svgeesus/EuroMPE/Polyphonic/voltage-ref-MAX6226ALA50+.md

# Voltage ref MAX6226ALA50+ 

New, hermetic ceramic LCC-8 package, may be replacing MAX6126AASA50+? Similar specs (but no ground sense, only output sense). Actually in stock at Mouser. $11.79/1

## Absolute initial accuracy

Initial accuracy 0.02% max = 1mV.

## Temperature

3ppm/°C (Max)

## Current / Load

Load regulation 5 (typ) 50 (max) μV/mA

## Long term drift

11ppm/1000hr

## Line regulation

Low dropout, 200mV, can run from 5.5V
