svgeesus/EuroMPE/Duophonic/notes.txt

High (120ms) latency on Teensy 4 with software MIDI-through
https://forum.pjrc.com/threads/65205-MIDI-Passthrough-Control-with-Op-Amp
