svgeesus/EuroMPE/data/oscillators/Tona.md

# Tona frequency analysis

## Tunng range (0V CV)

Coarse mid-way,
    fine mid-way, no external CV
        778.9Hz sd 1.8Hz
        G5 minus 11 cents
        maybe picking up periodic interference from nearby phaser.

    fine at min
        662.0Hz, sd 43mHz
        E5 plus 7 cents

    fine at max
        924.6Hz, sd 65mHz
        A#5 minus 14 cents

    fine range log2(f2/f1) =

Coarse at min
    fine at min, no ext CV
        2.40Hz, sd 66mHz
        D#-3 minus 22 cents

Coarse at max
    fine at max
        66.15kHz, sd 8.6
        rising trend,
