svgeesus/EuroMPE/data/oscillators/A111-3.md

# Doepfer A111-3 VCO

0.0030V 31.99896Hz  -> 5 octaves up is 1023.96672Hz
5.0030V 1022288Hz
1023.9963 at 5.0055V

5.0025 / 5 = 1.0005 V/octaves
