svgeesus/EuroMPE/data/oscillators/Dixie2plus.md

# Intellijel Dixie 2+ VCO

Warmed > 24 hours.

T=24.5C

0.0094V 31.99636Hz  -> 5 octaves up is 1023.88352Hz
5.0094V 1029.656Hz
1024.0593 at 5.0016V (too high, check for closer to 1023.88352Hz)

4.9922 / 5 = 0.99844 V/octaves
