svgeesus/EuroMPE/data/oscillators/Dixie2-audiorange.png

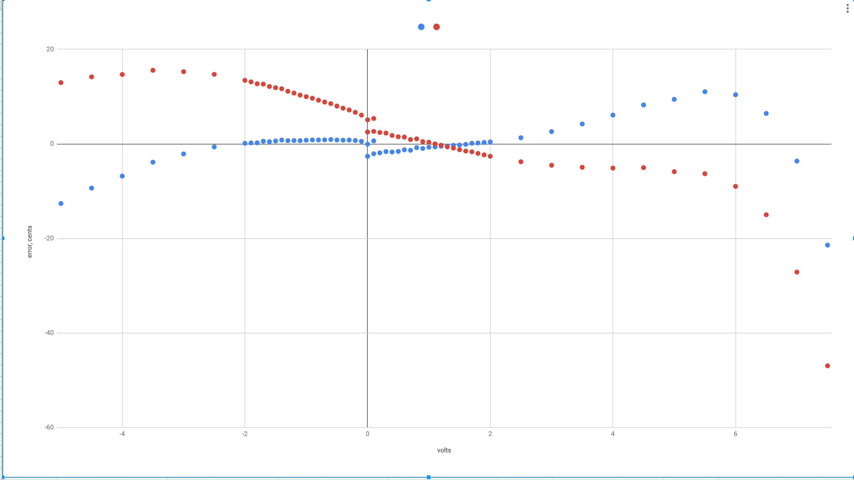
data/oscillators/Dixie2-audiorange.png
