svgeesus/EuroMPE/data/oscillators/Dixie2-fullrange.png

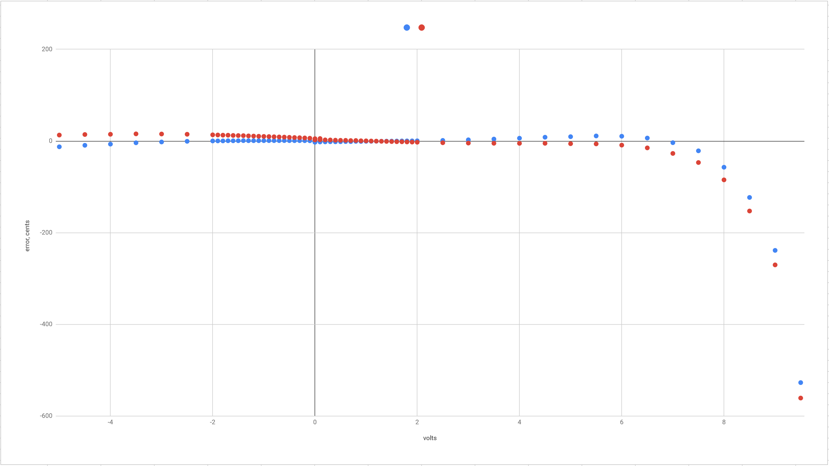
data/oscillators/Dixie2-fullrange.png
