svgeesus/EuroMPE/data/oscillators/Tona HF warmedup.png

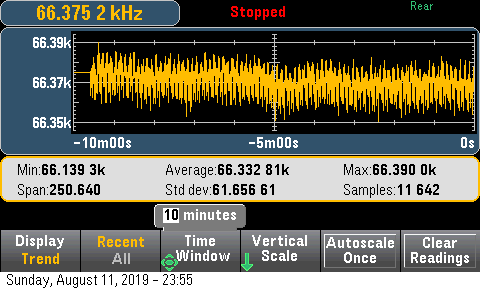
data/oscillators/Tona HF warmedup.png
