svgeesus/EuroMPE/Duophonic/img/10R.png

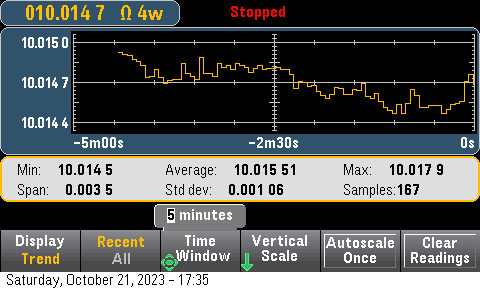
Duophonic/img/10R.png
