svgeesus/EuroMPE/Duophonic/img/1236-2-neg-next37hr.png

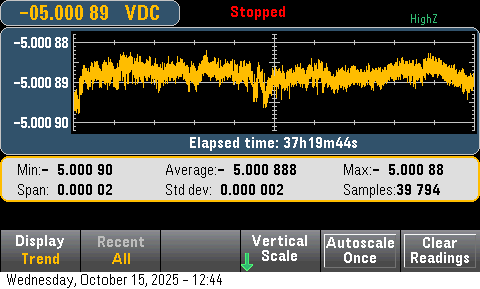
Duophonic/img/1236-2-neg-next37hr.png
