svgeesus/EuroMPE/Duophonic/img/1236-neg-13h.png

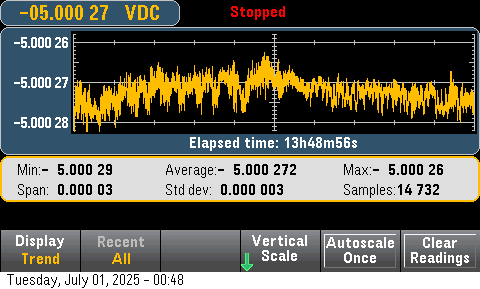
Duophonic/img/1236-neg-13h.png
