svgeesus/EuroMPE/Duophonic/img/adafruit-soft-touch-push.png

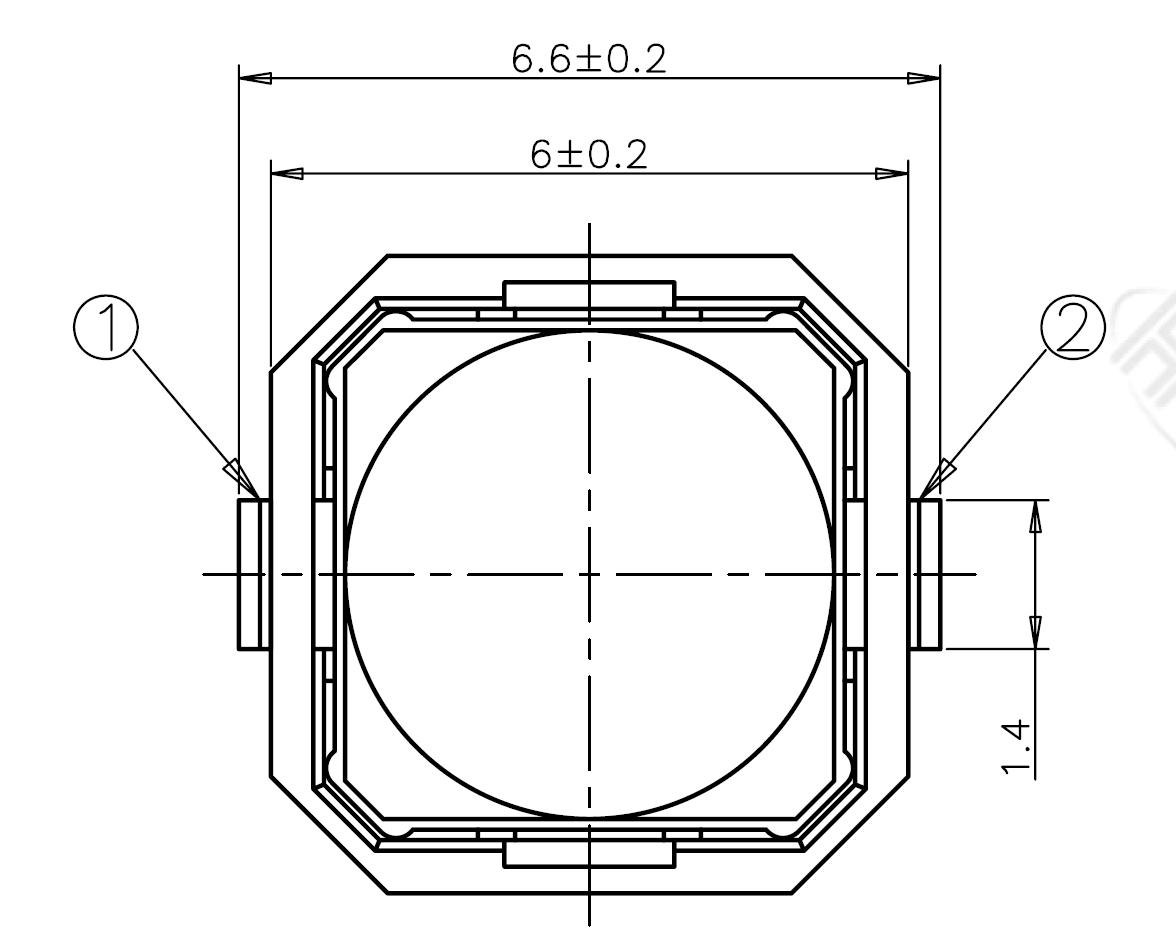
Duophonic/img/adafruit-soft-touch-push.png
