svgeesus/EuroMPE/Duophonic/img/Adafruit-USB-B-panel.png

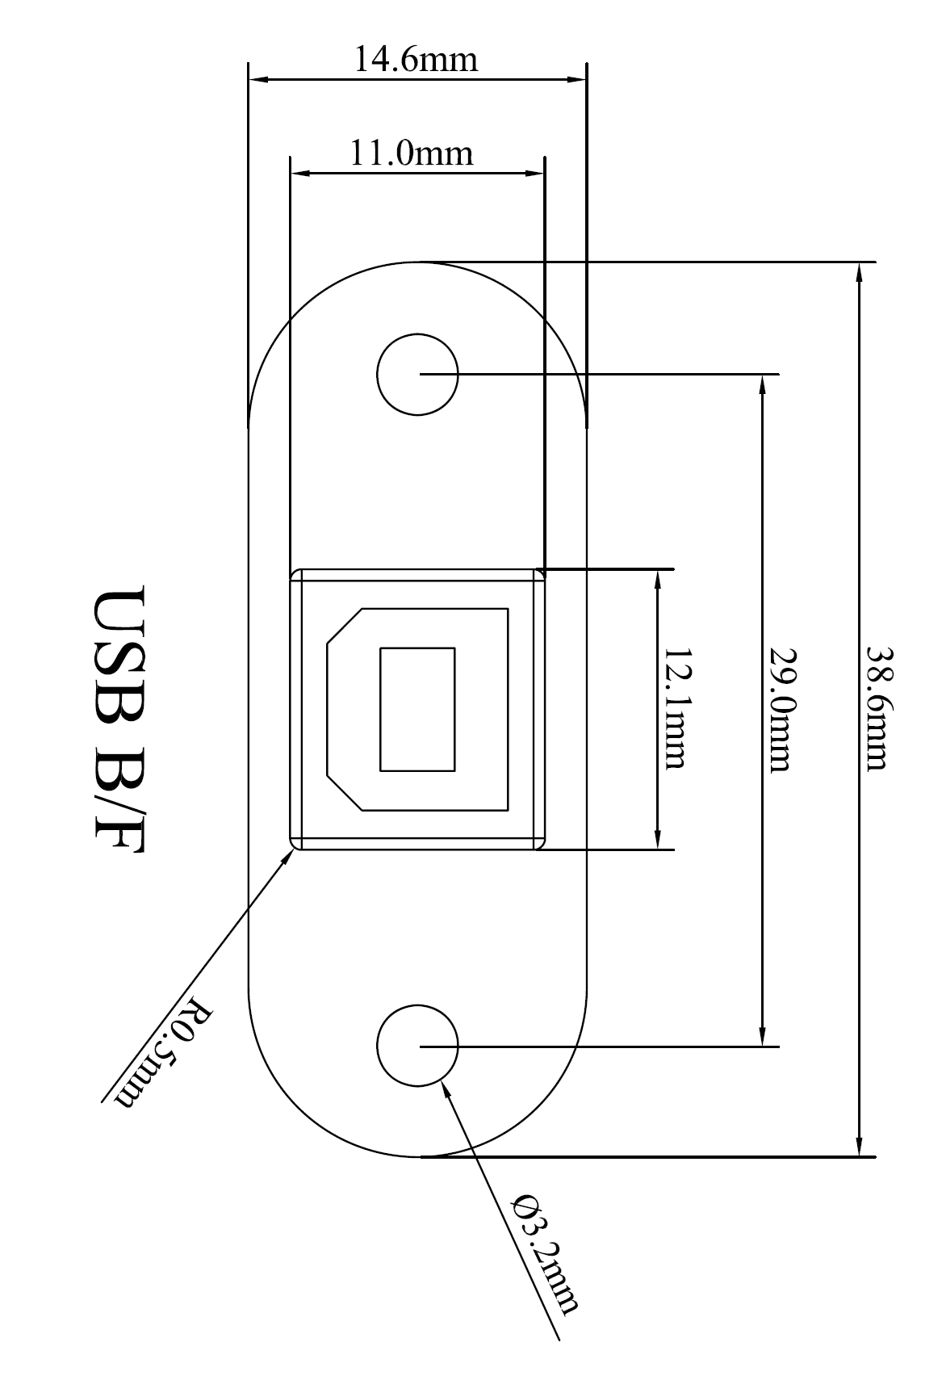
Duophonic/img/Adafruit-USB-B-panel.png
