svgeesus/EuroMPE/Duophonic/img/Adafruit-USB-B-photo.jpg

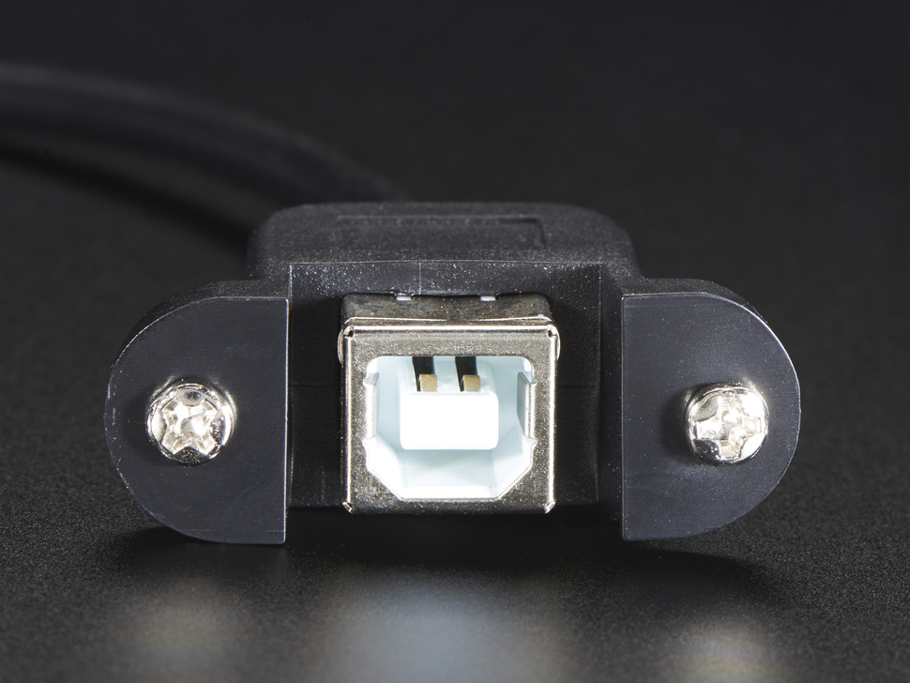
Duophonic/img/Adafruit-USB-B-photo.jpg
