svgeesus/EuroMPE/Duophonic/img/analogled.jpg

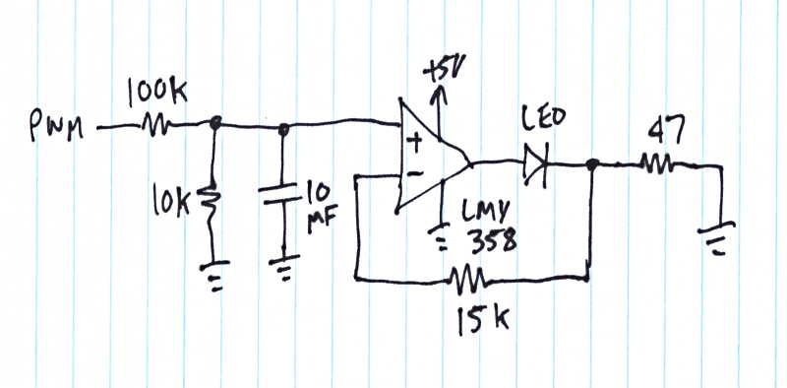
Duophonic/img/analogled.jpg
