svgeesus/EuroMPE/Duophonic/img/CKtactile.png

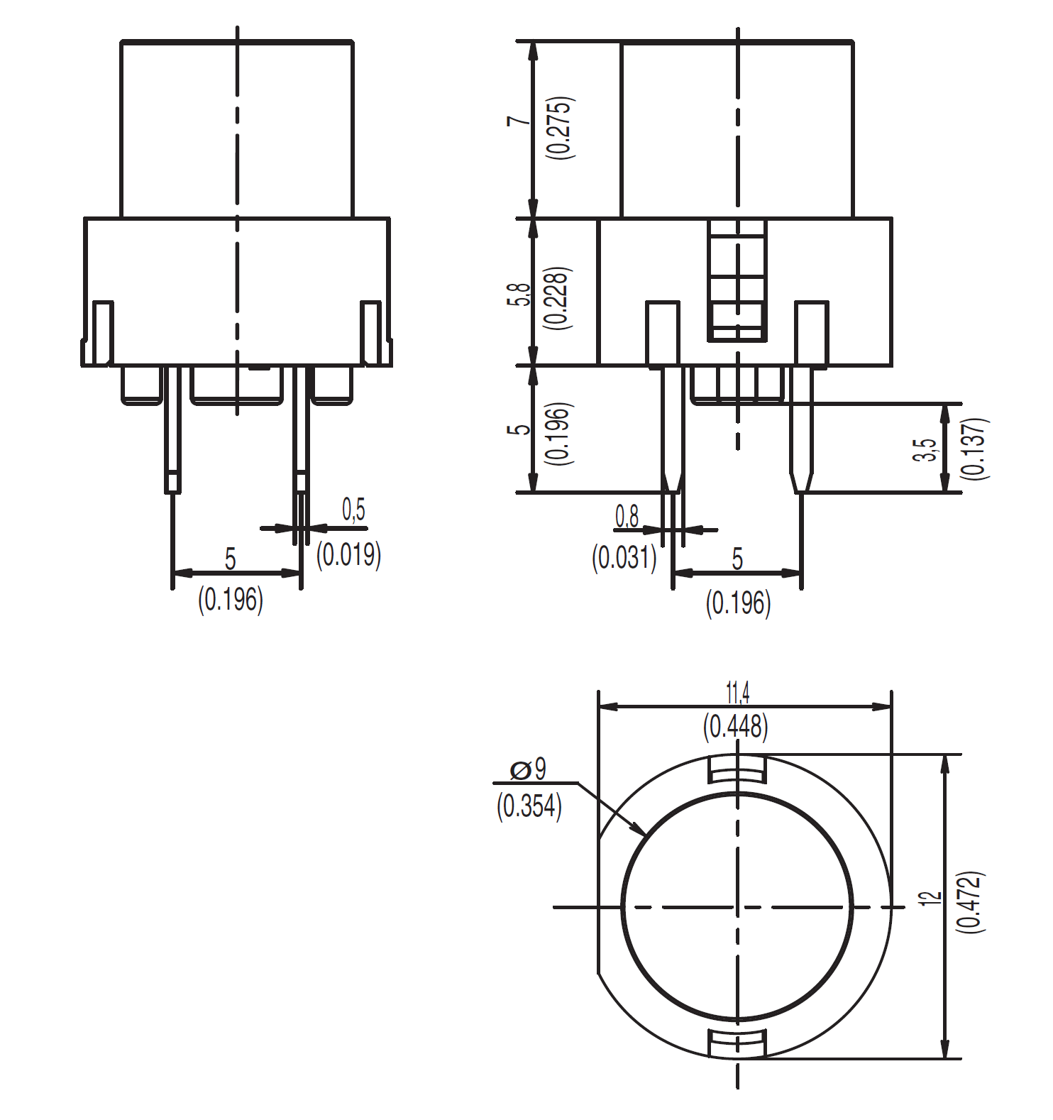
Duophonic/img/CKtactile.png
