svgeesus/EuroMPE/Duophonic/img/cvout-6n8-10k-200p.png

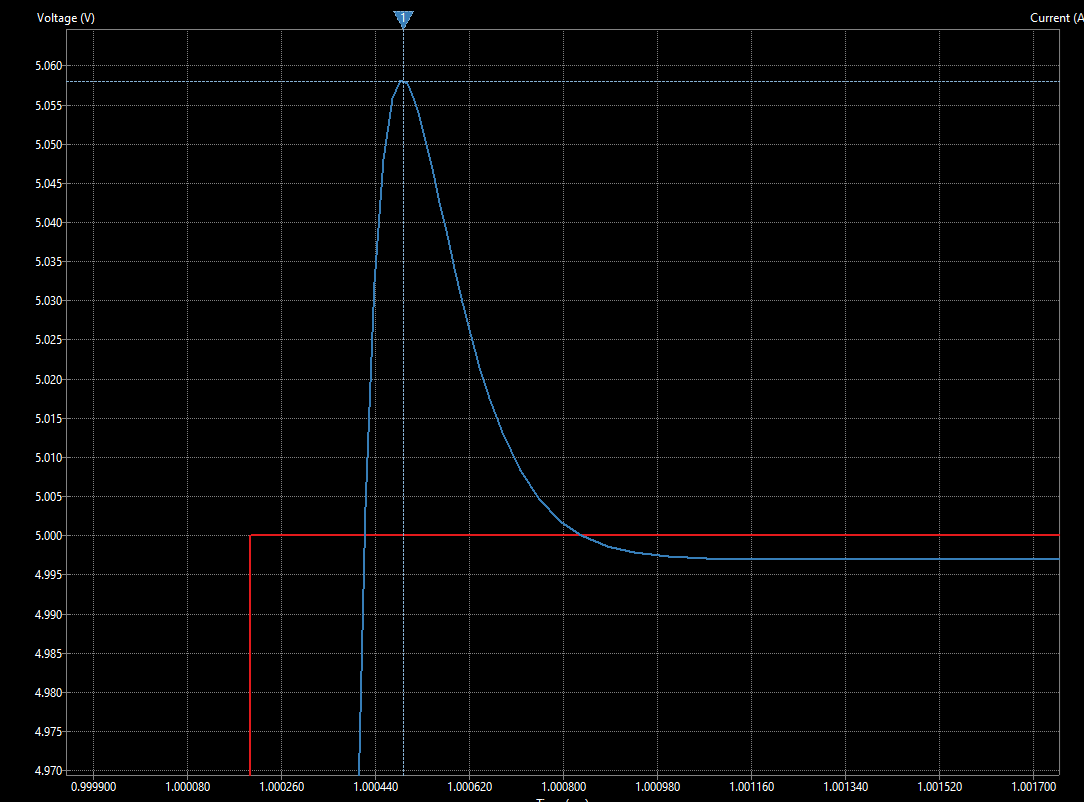
Duophonic/img/cvout-6n8-10k-200p.png
