svgeesus/EuroMPE/Duophonic/img/cvout-100n-200pF.png

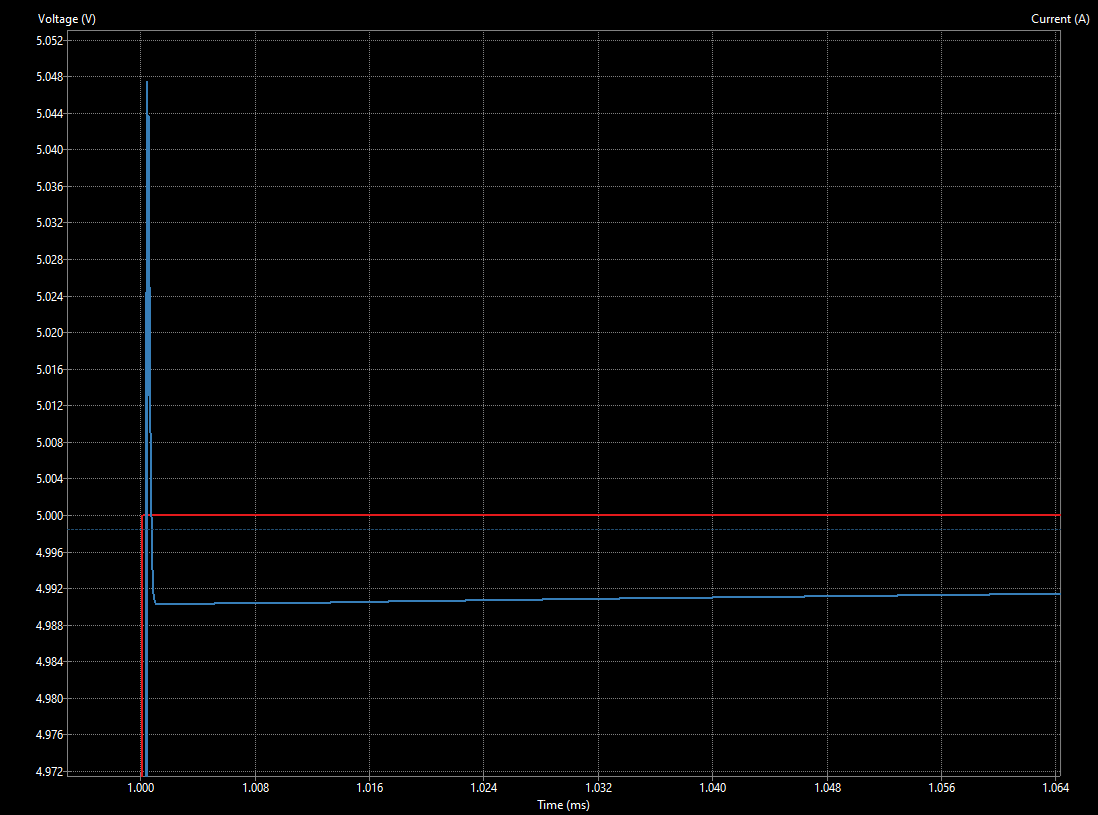
Duophonic/img/cvout-100n-200pF.png
