svgeesus/EuroMPE/Duophonic/img/DAC8168-14-pinout.png

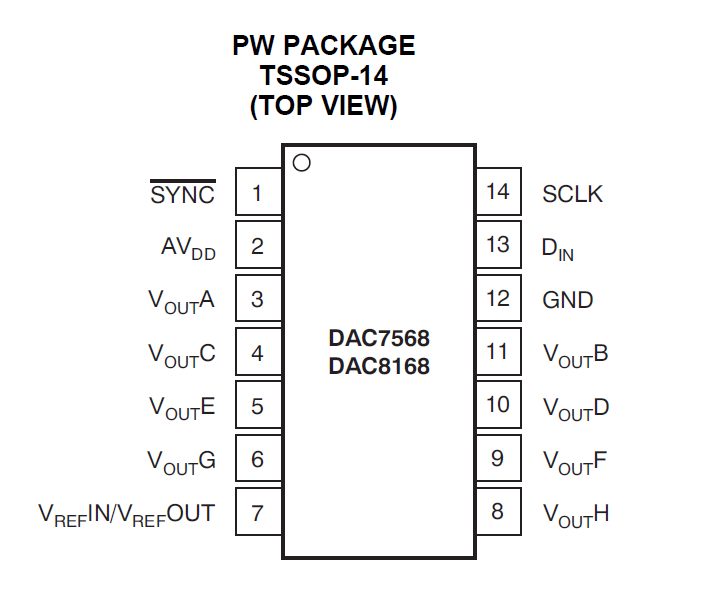
Duophonic/img/DAC8168-14-pinout.png
