svgeesus/EuroMPE/Duophonic/img/Encoder-Sparkfun-RGB.png

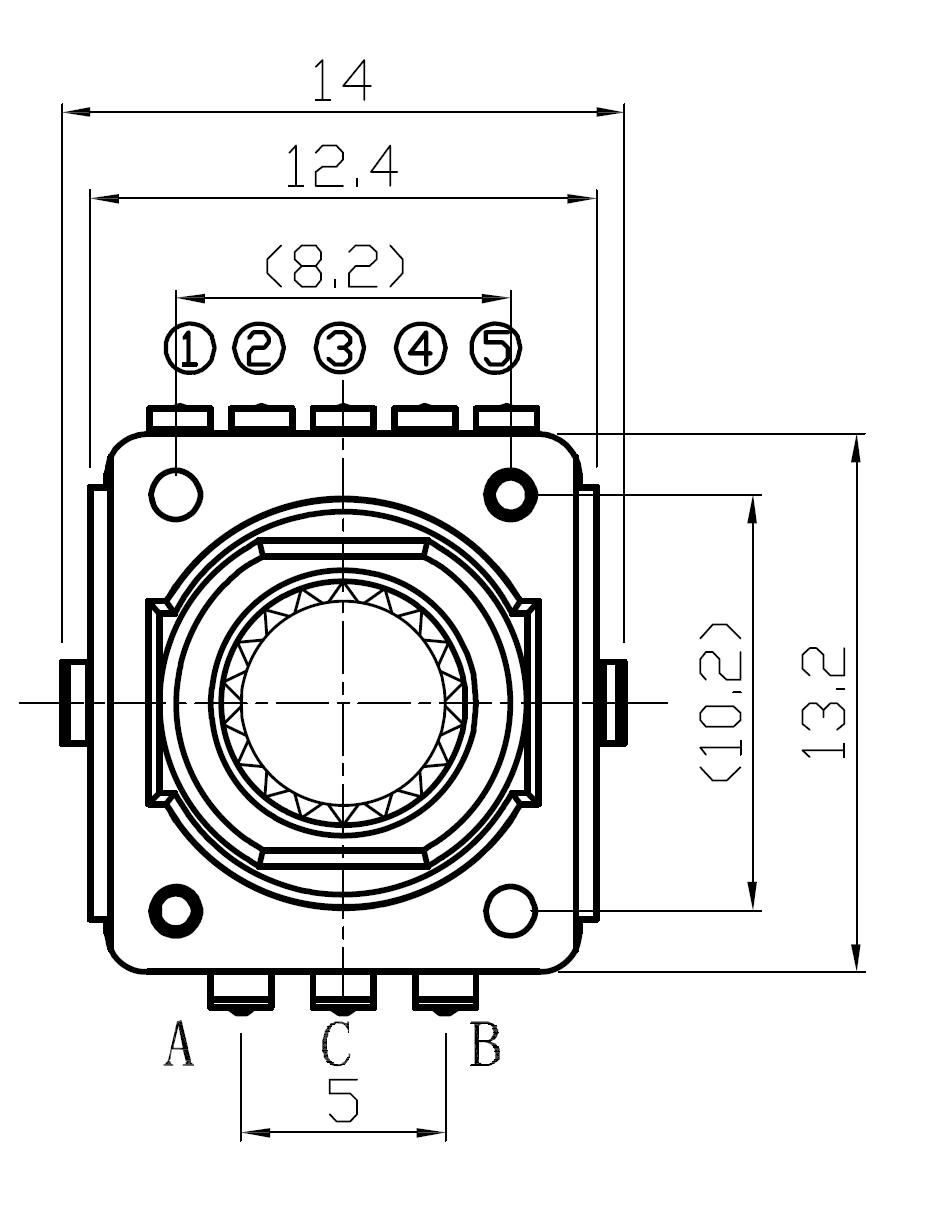
Duophonic/img/Encoder-Sparkfun-RGB.png
