svgeesus/EuroMPE/Duophonic/img/FD-115TRGB.png

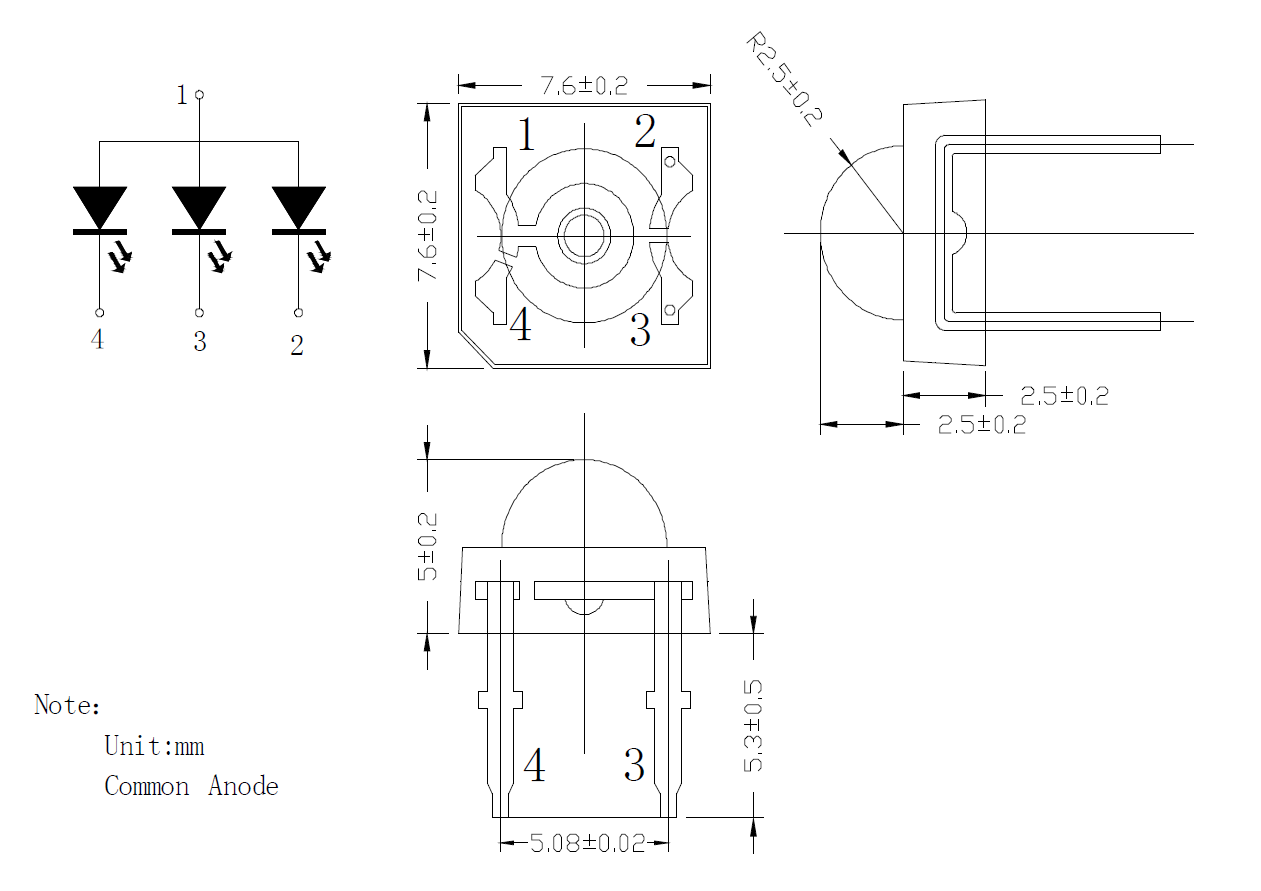
Duophonic/img/FD-115TRGB.png
