svgeesus/EuroMPE/Duophonic/img/front.png

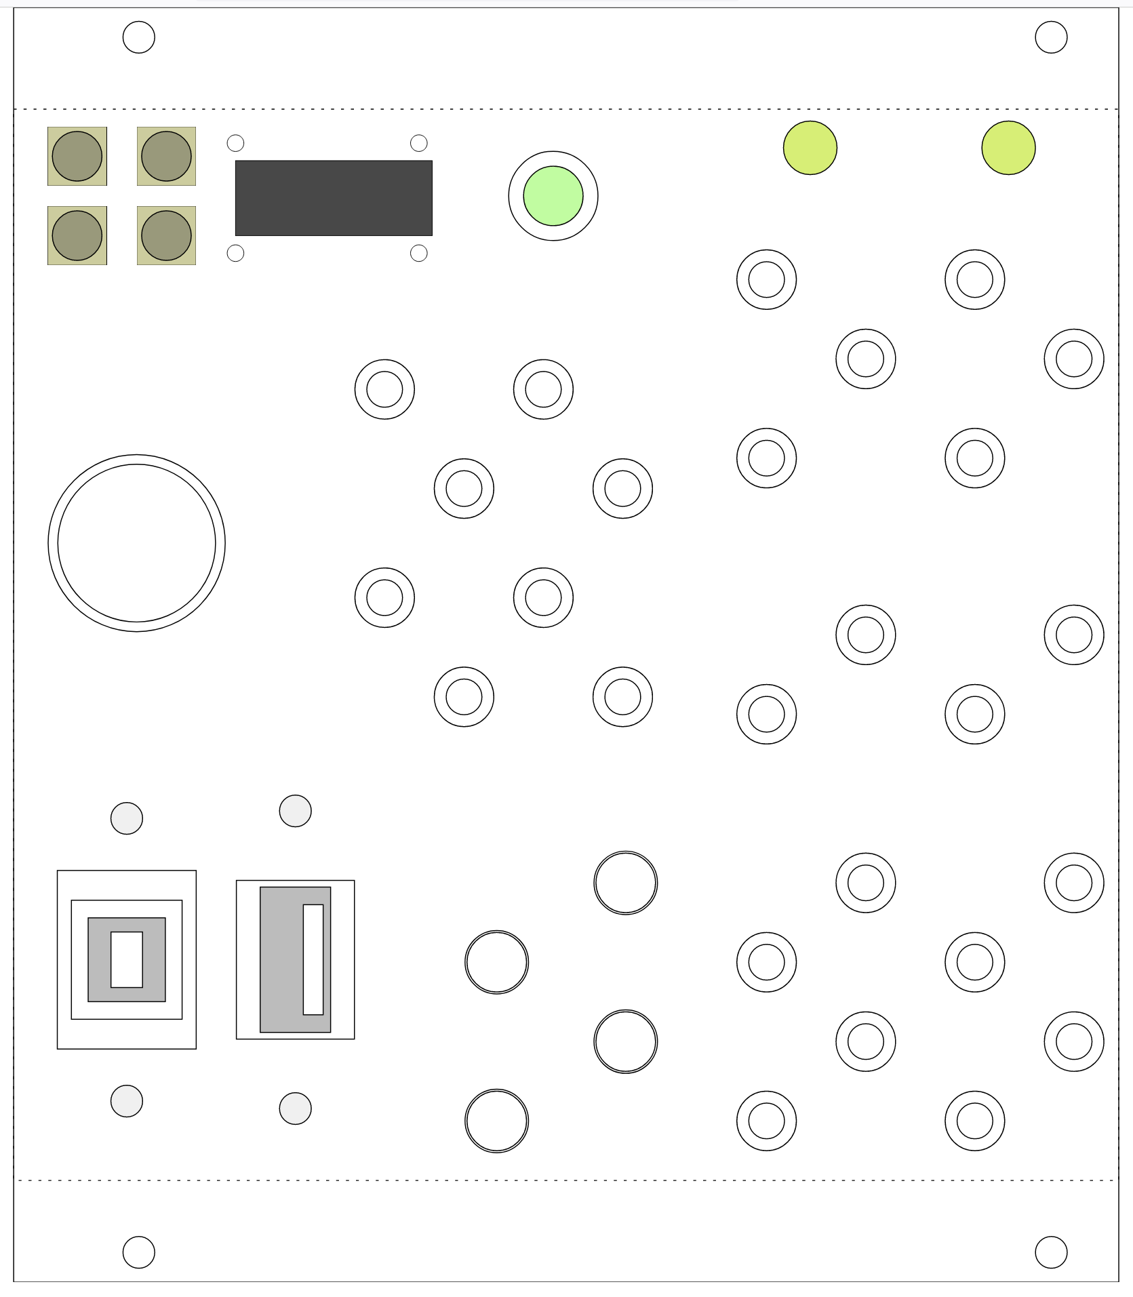
Duophonic/img/front.png
