svgeesus/EuroMPE/Duophonic/img/LS8-trim-circuit.png

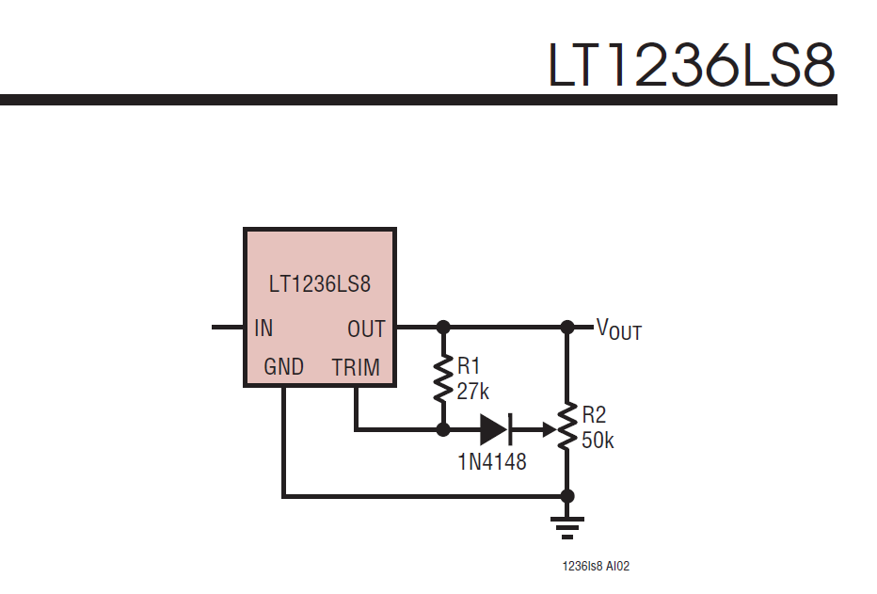
Duophonic/img/LS8-trim-circuit.png
