svgeesus/EuroMPE/Duophonic/img/LS8-trim-text.png

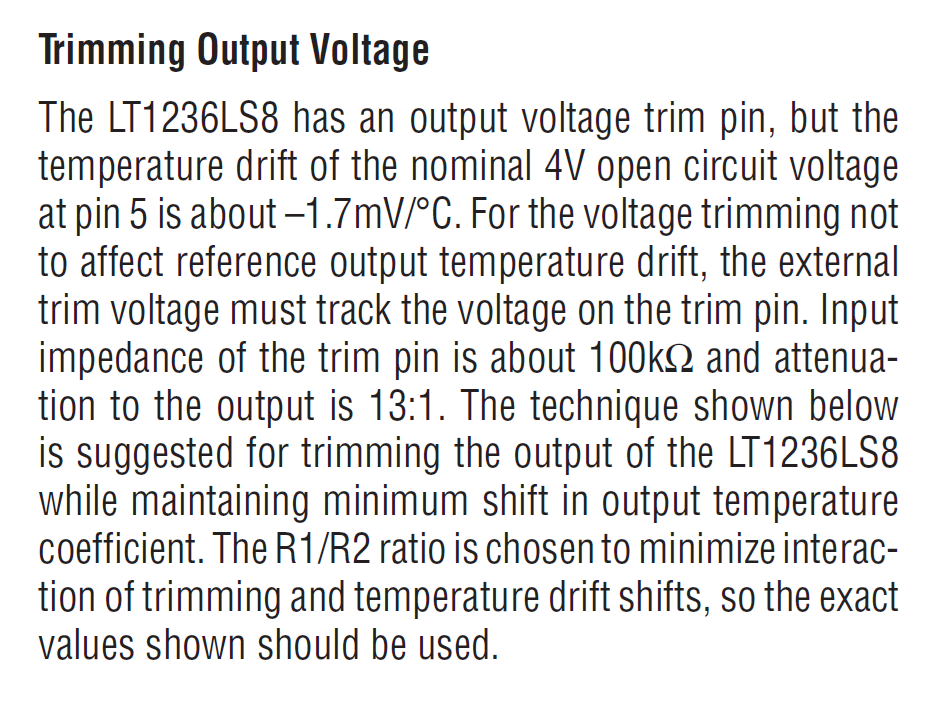
Duophonic/img/LS8-trim-text.png
