svgeesus/EuroMPE/Duophonic/img/MPU-mockup.png

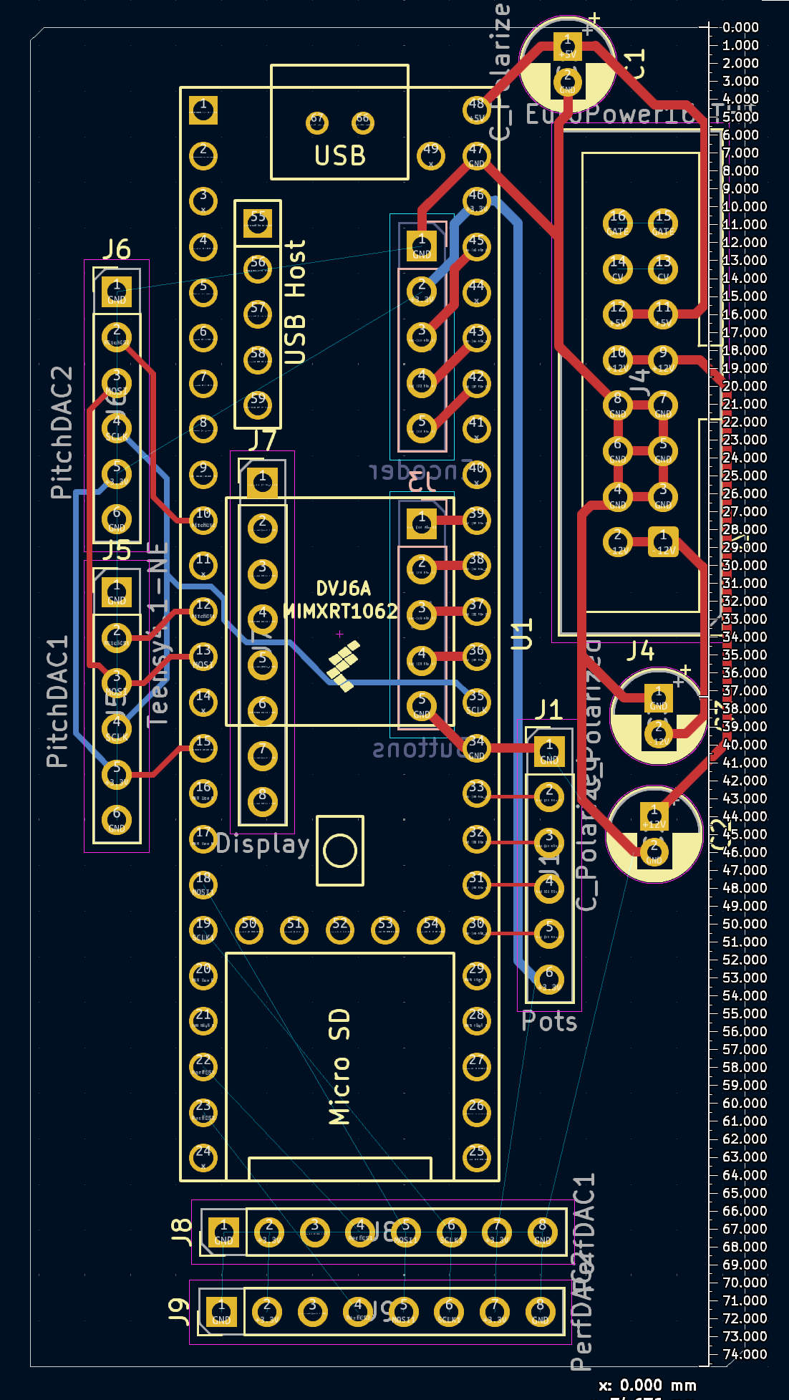
Duophonic/img/MPU-mockup.png
