svgeesus/EuroMPE/Duophonic/img/O_C-T41 output_buffer.png

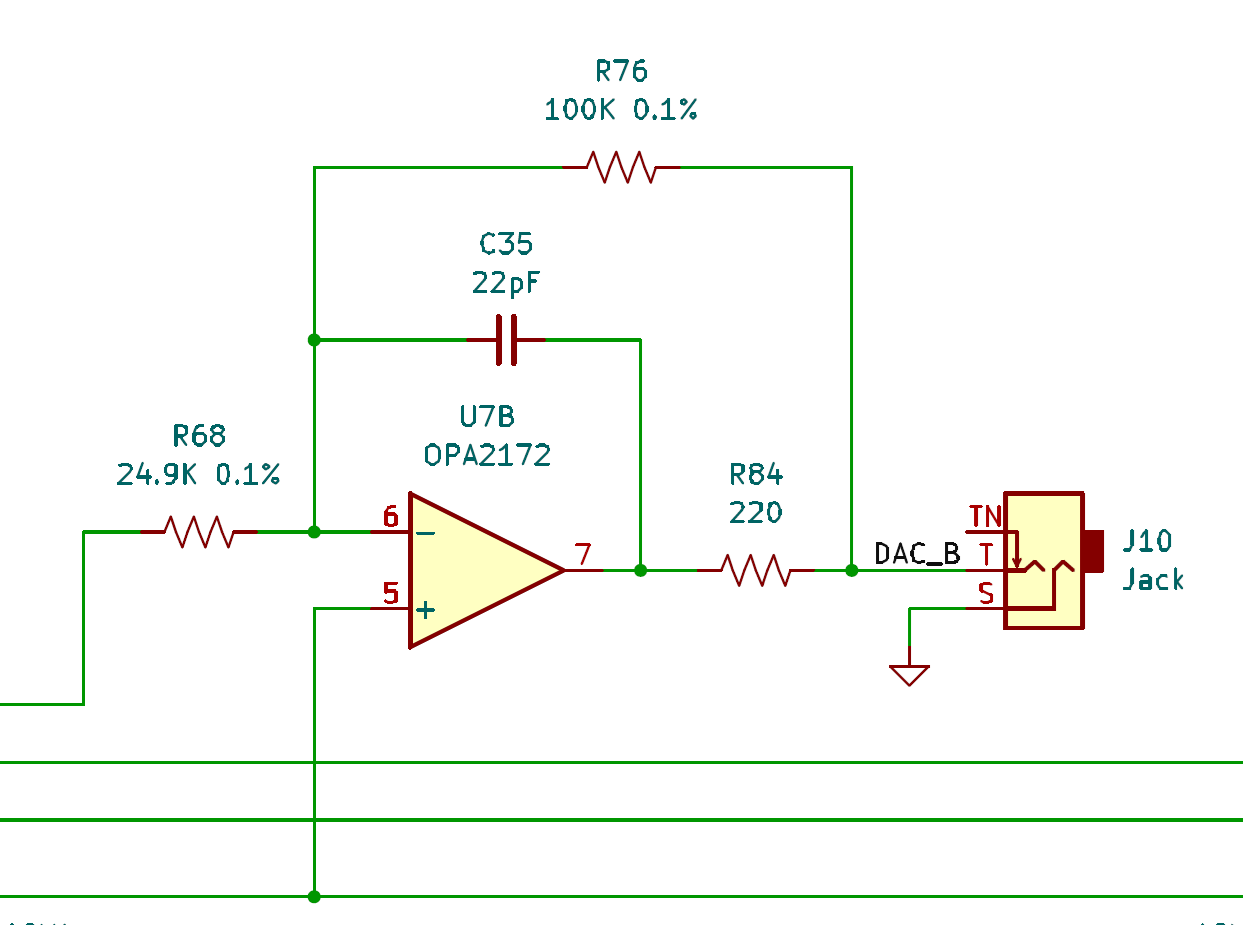
Duophonic/img/O_C-T41 output_buffer.png
