svgeesus/EuroMPE/Duophonic/img/oled-panel.png

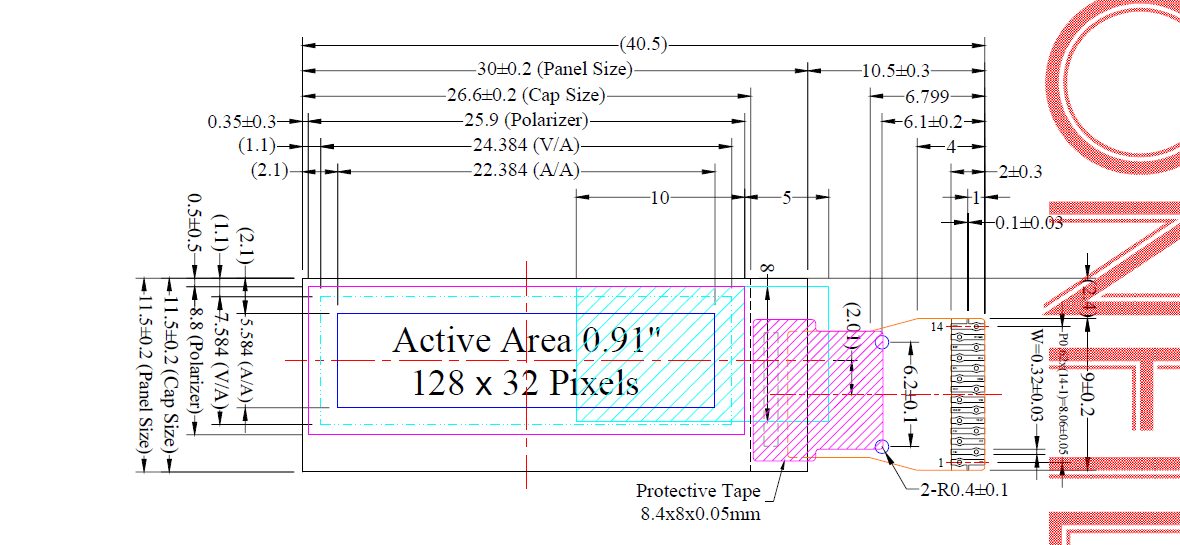
Duophonic/img/oled-panel.png
