svgeesus/EuroMPE/Duophonic/img/PerfDAC-v2-bottom-osh.png

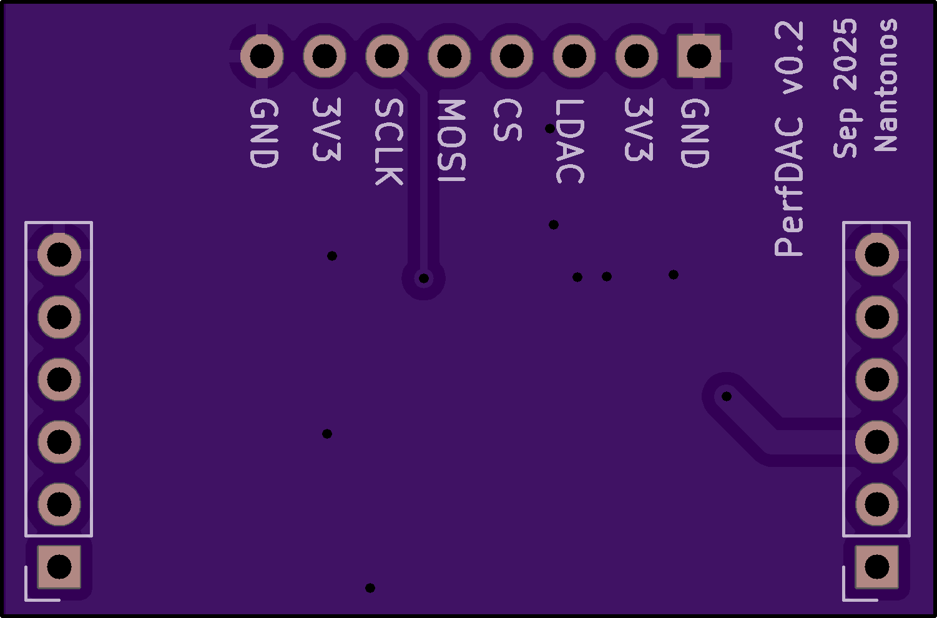
Duophonic/img/PerfDAC-v2-bottom-osh.png
