svgeesus/EuroMPE/Duophonic/img/PerfDAC-v2-top-osh.png

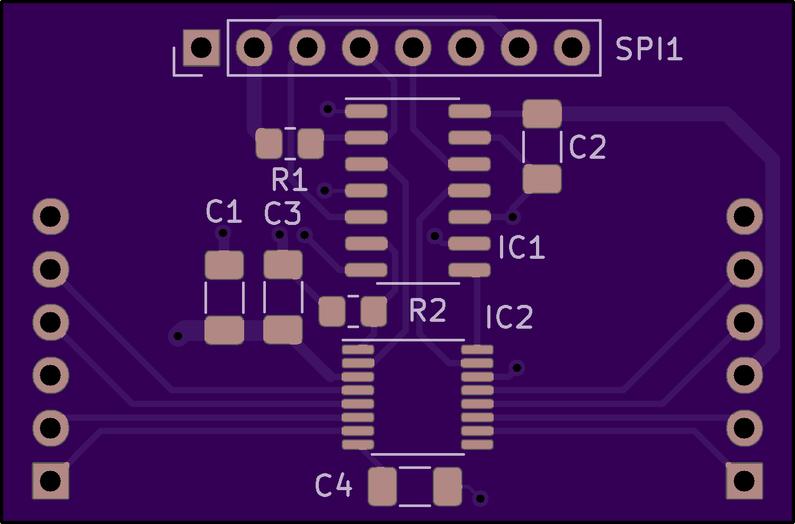
Duophonic/img/PerfDAC-v2-top-osh.png
