svgeesus/EuroMPE/Duophonic/img/pinout-41.png

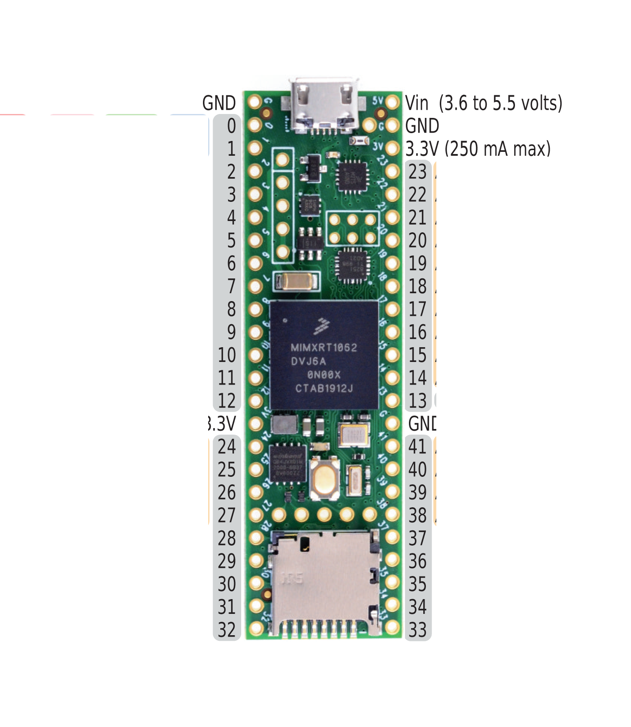
Duophonic/img/pinout-41.png
