svgeesus/EuroMPE/Duophonic/img/pitchdac-board.png

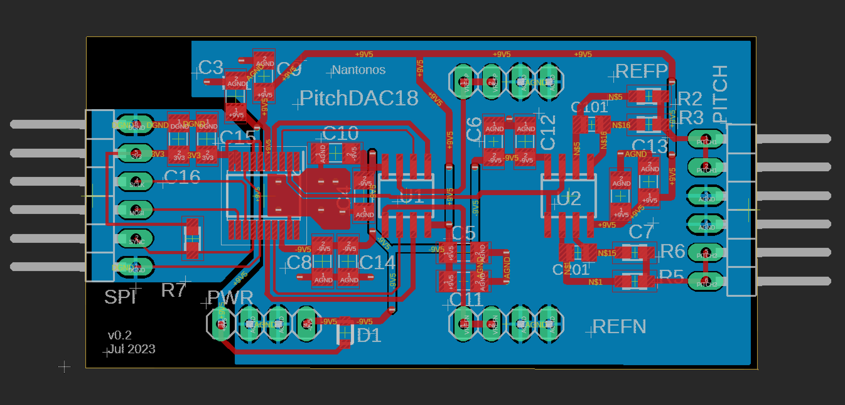
Duophonic/img/pitchdac-board.png
