svgeesus/EuroMPE/Duophonic/img/pitchdac-schematic-v04.png

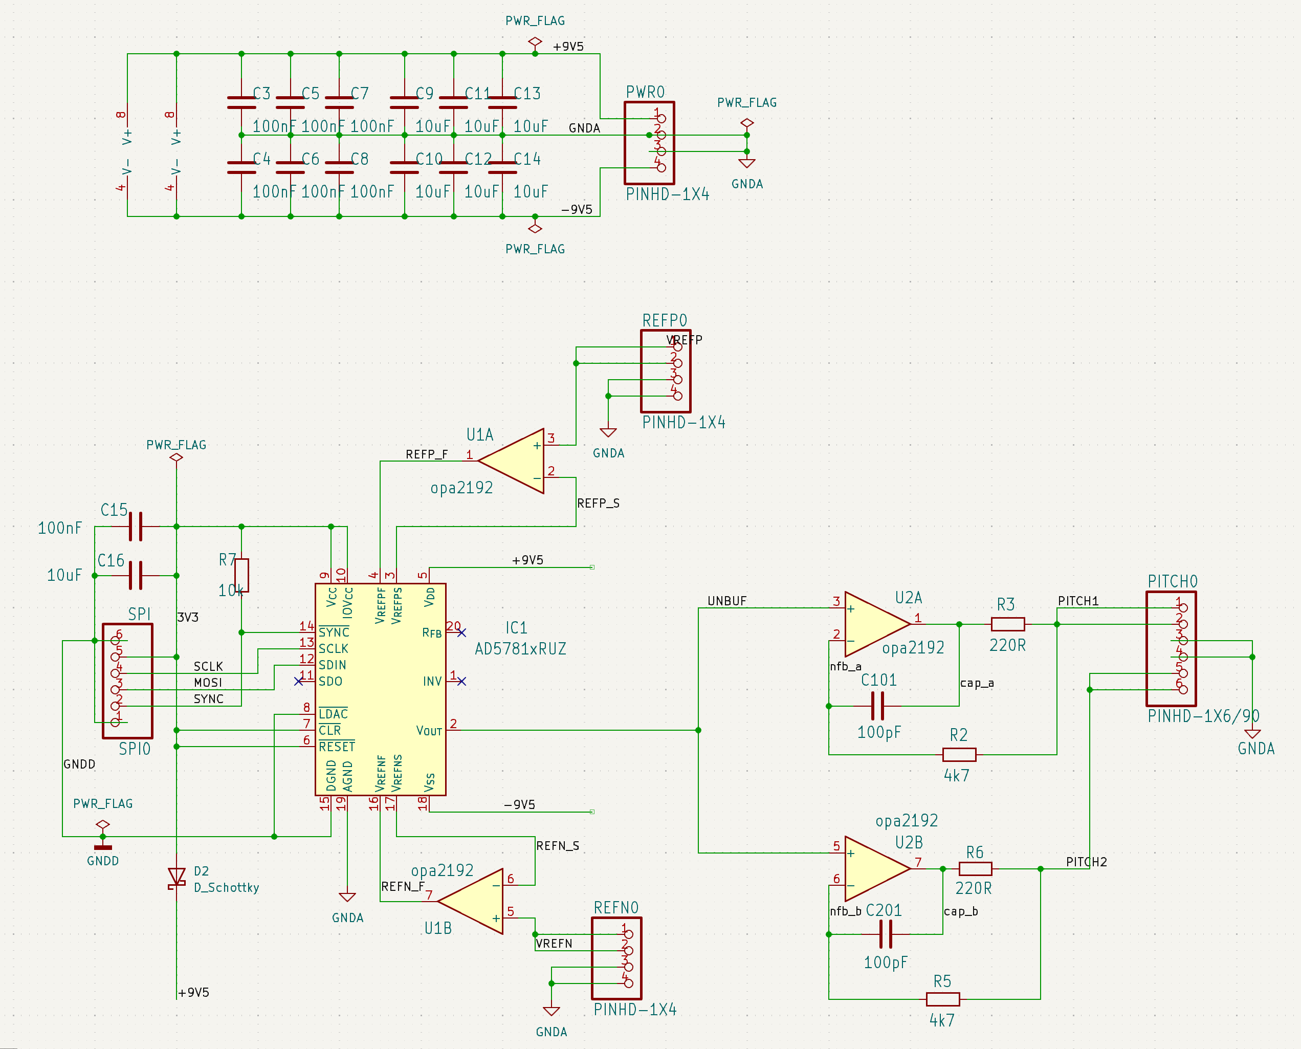
Duophonic/img/pitchdac-schematic-v04.png
