svgeesus/EuroMPE/Duophonic/img/pitchdac-top-osh.png

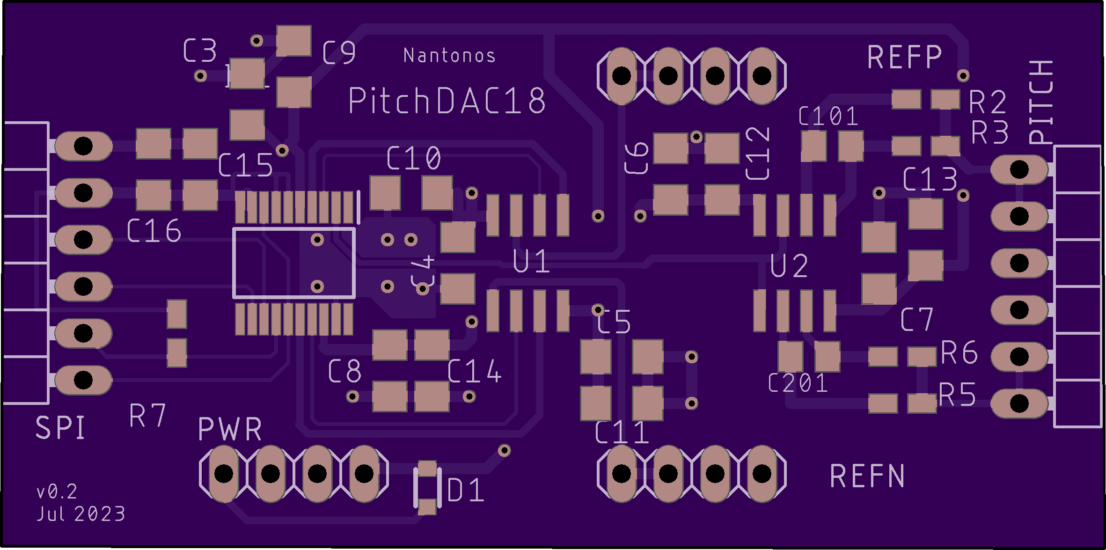
Duophonic/img/pitchdac-top-osh.png
