svgeesus/EuroMPE/Duophonic/img/power-osh-back.png

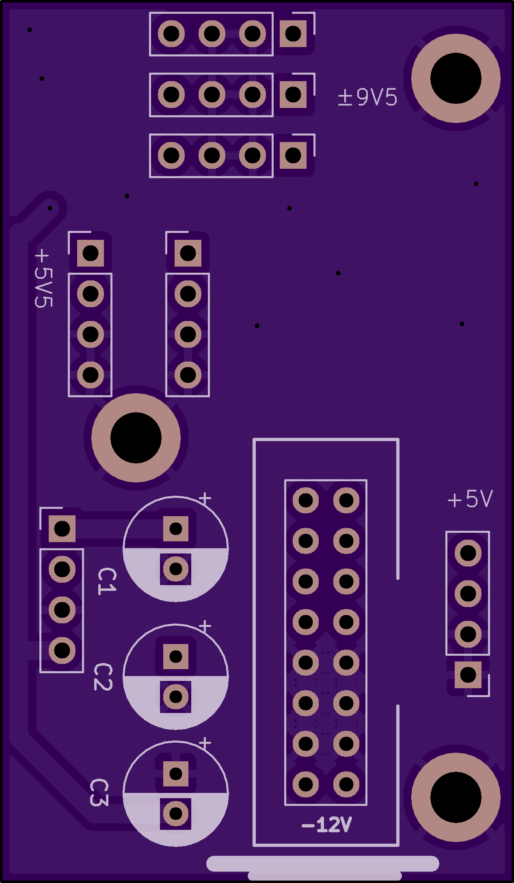
Duophonic/img/power-osh-back.png
