svgeesus/EuroMPE/Duophonic/img/power-osh-front.png

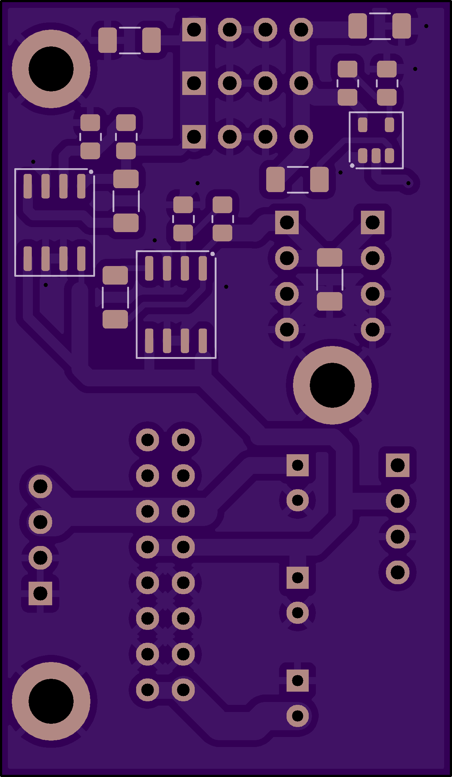
Duophonic/img/power-osh-front.png
