svgeesus/EuroMPE/Duophonic/img/psu-5min.png

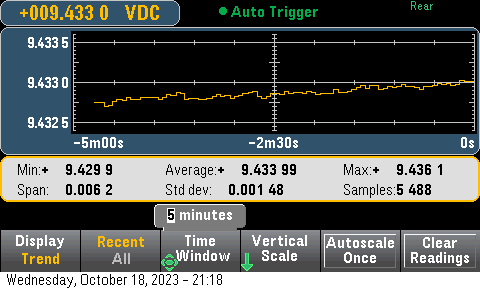
Duophonic/img/psu-5min.png
