svgeesus/EuroMPE/Duophonic/img/PWM-highest.png

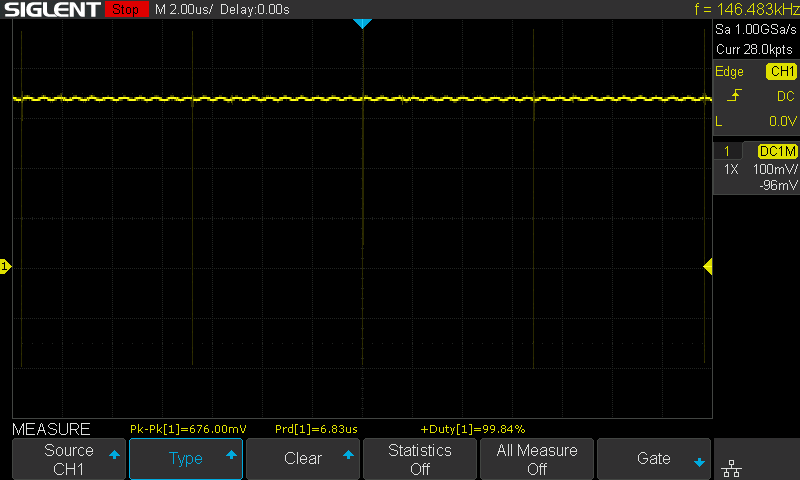
Duophonic/img/PWM-highest.png
