svgeesus/EuroMPE/Duophonic/img/PWM-lowest.png

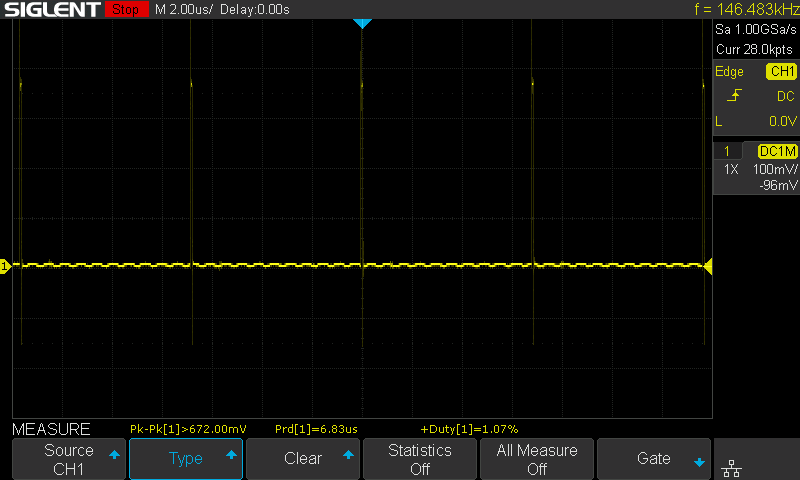
Duophonic/img/PWM-lowest.png
