svgeesus/EuroMPE/Duophonic/img/PWM.png

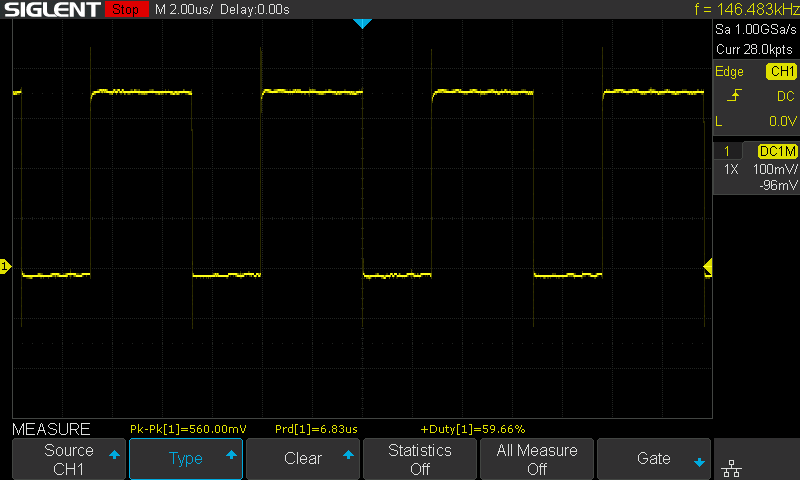
Duophonic/img/PWM.png
