svgeesus/EuroMPE/Duophonic/img/song-huei-stp-product.jpg

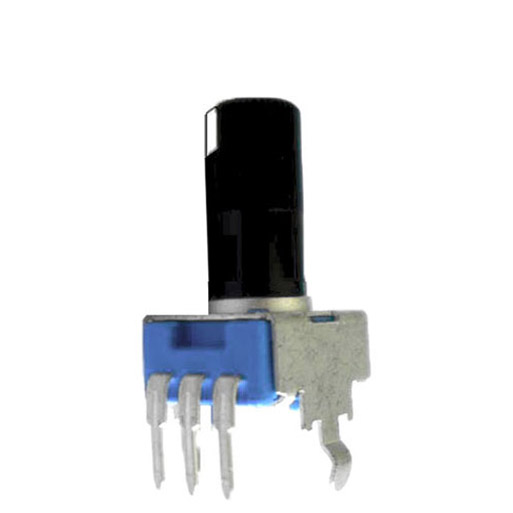
Duophonic/img/song-huei-stp-product.jpg
