svgeesus/EuroMPE/Duophonic/img/tact.png

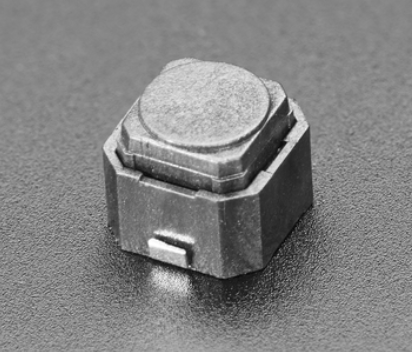
Duophonic/img/tact.png
