svgeesus/EuroMPE/Duophonic/img/Teensy4.1-logical.png

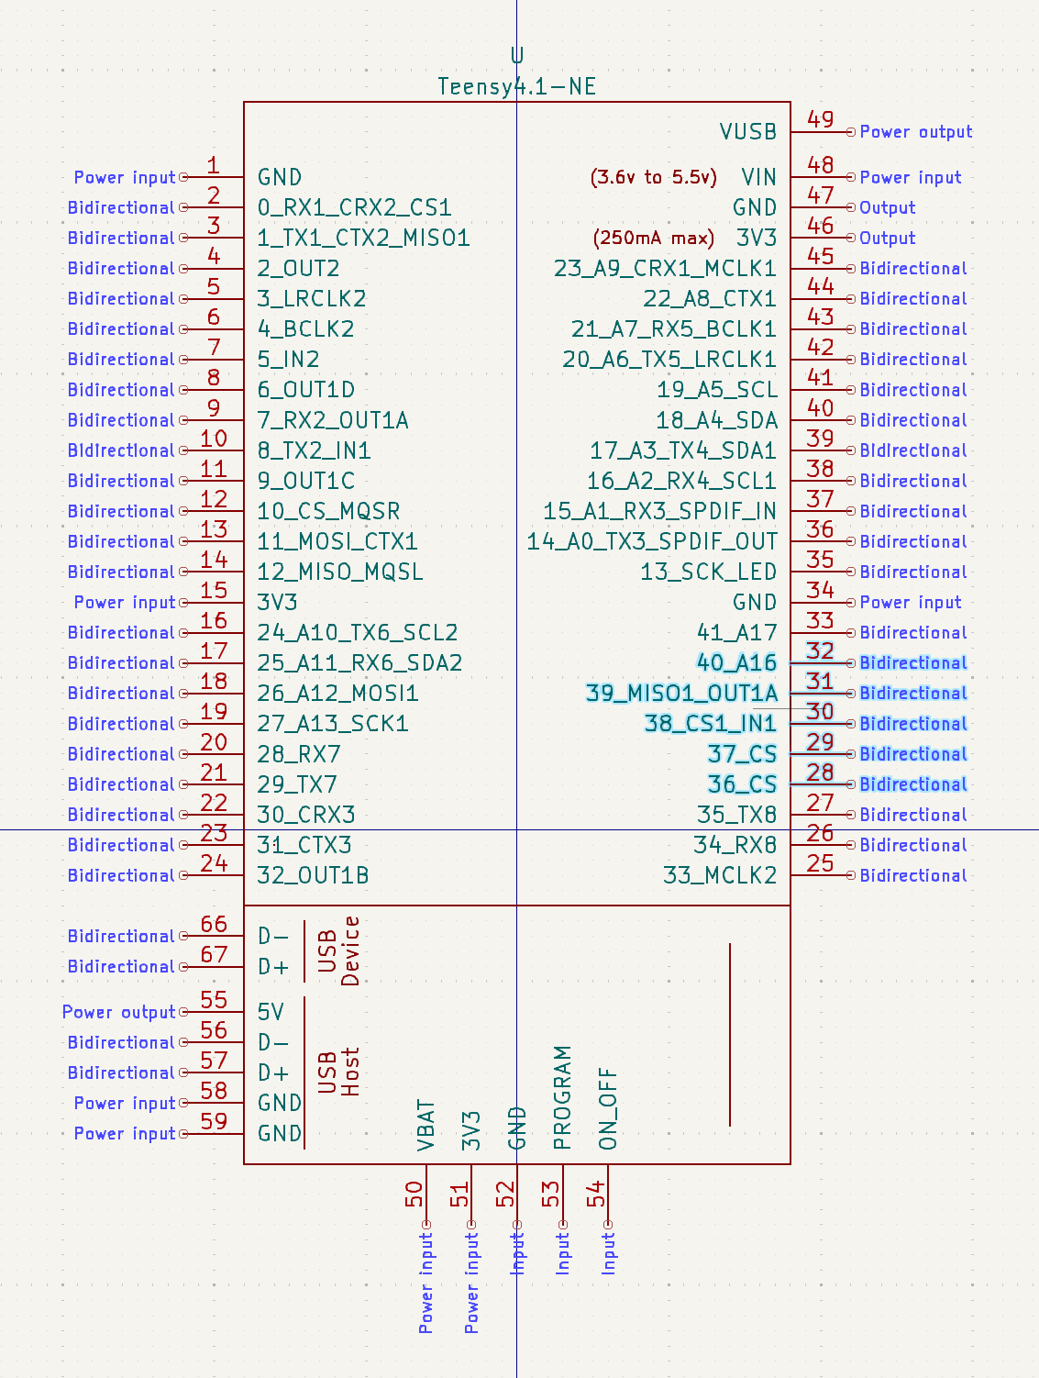
Duophonic/img/Teensy4.1-logical.png
