svgeesus/EuroMPE/Duophonic/img/Teensy4.1-physical.png

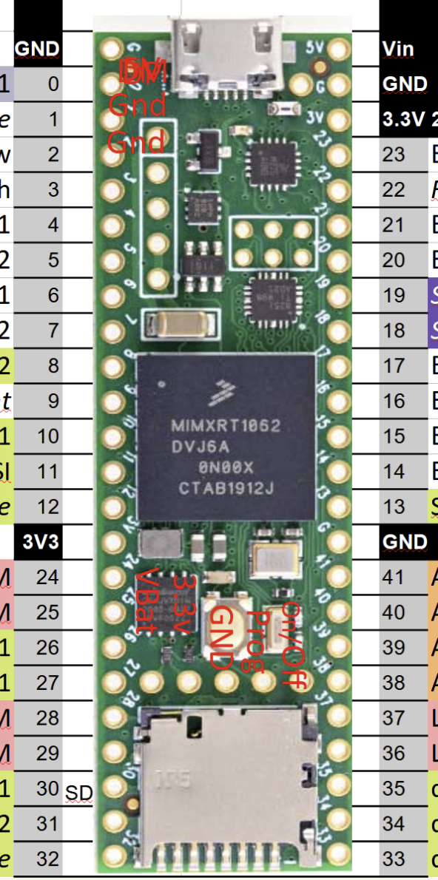
Duophonic/img/Teensy4.1-physical.png
