svgeesus/EuroMPE/Duophonic/img/Teensy41.jpg

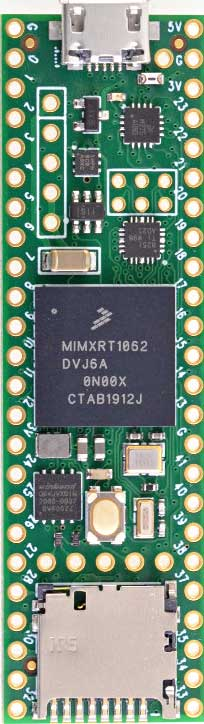
Duophonic/img/Teensy41.jpg
