svgeesus/EuroMPE/Duophonic/img/Thonk-encoder-knobs.png

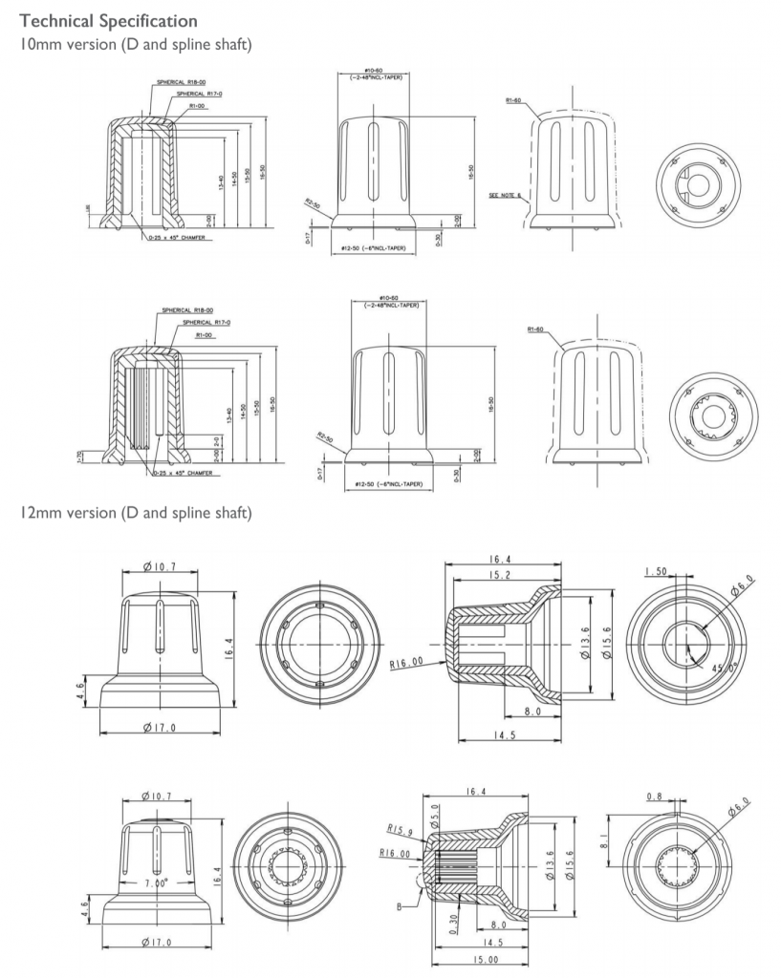
Duophonic/img/Thonk-encoder-knobs.png
