svgeesus/EuroMPE/Duophonic/img/top-left-mounting-hole.png

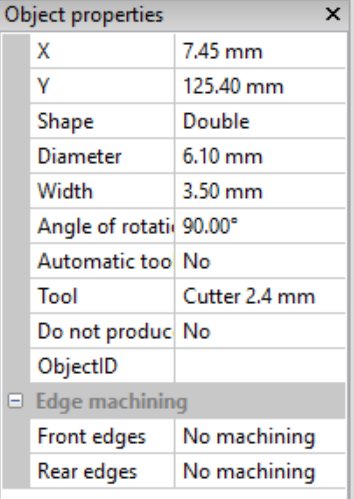
Duophonic/img/top-left-mounting-hole.png
