svgeesus/EuroMPE/Duophonic/img/USB-A-panel.png

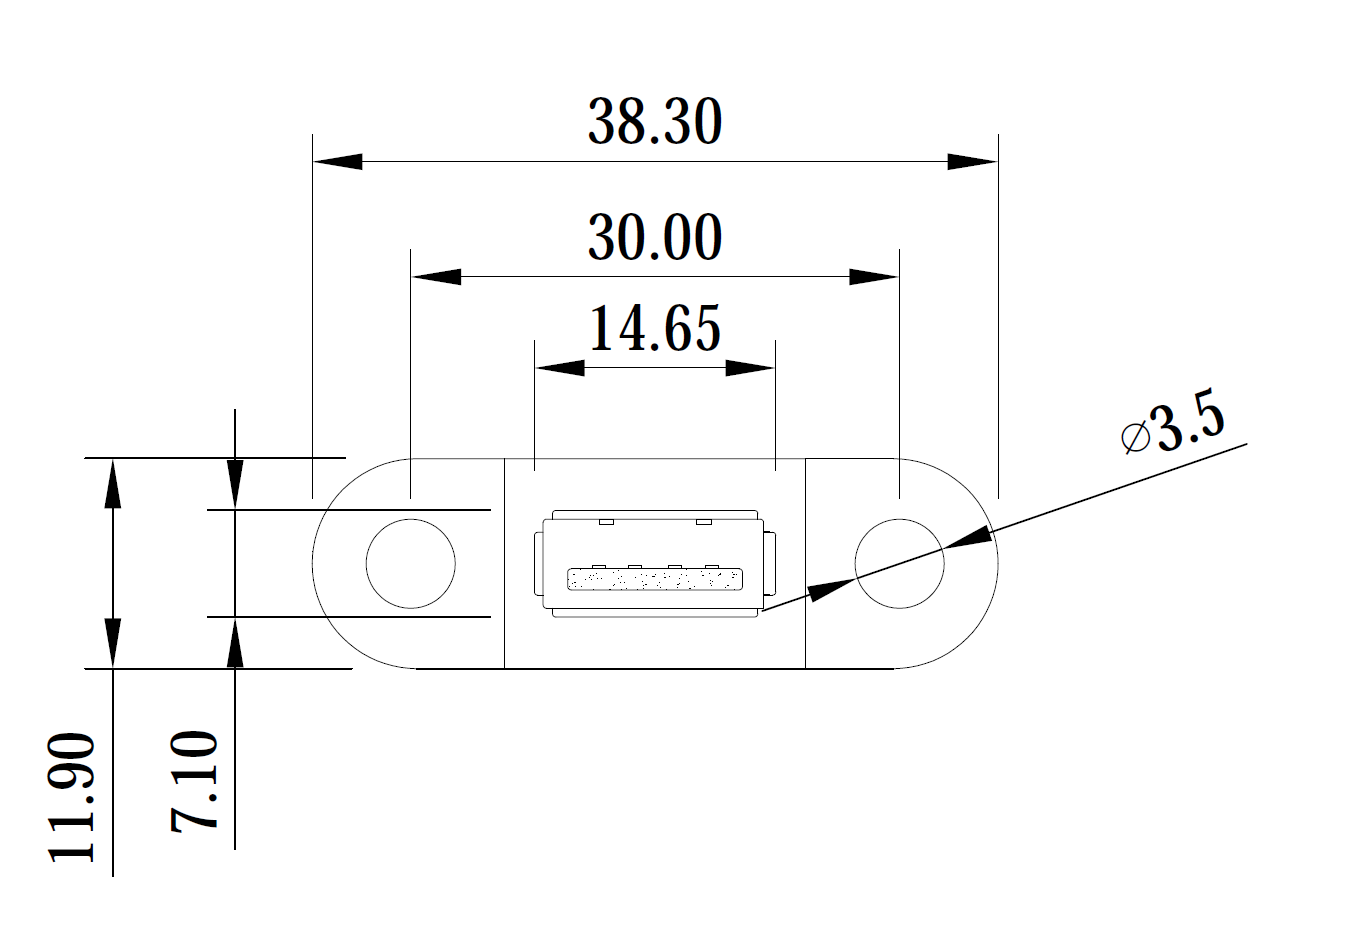
Duophonic/img/USB-A-panel.png
