svgeesus/EuroMPE/Duophonic/img/USB-panel.png

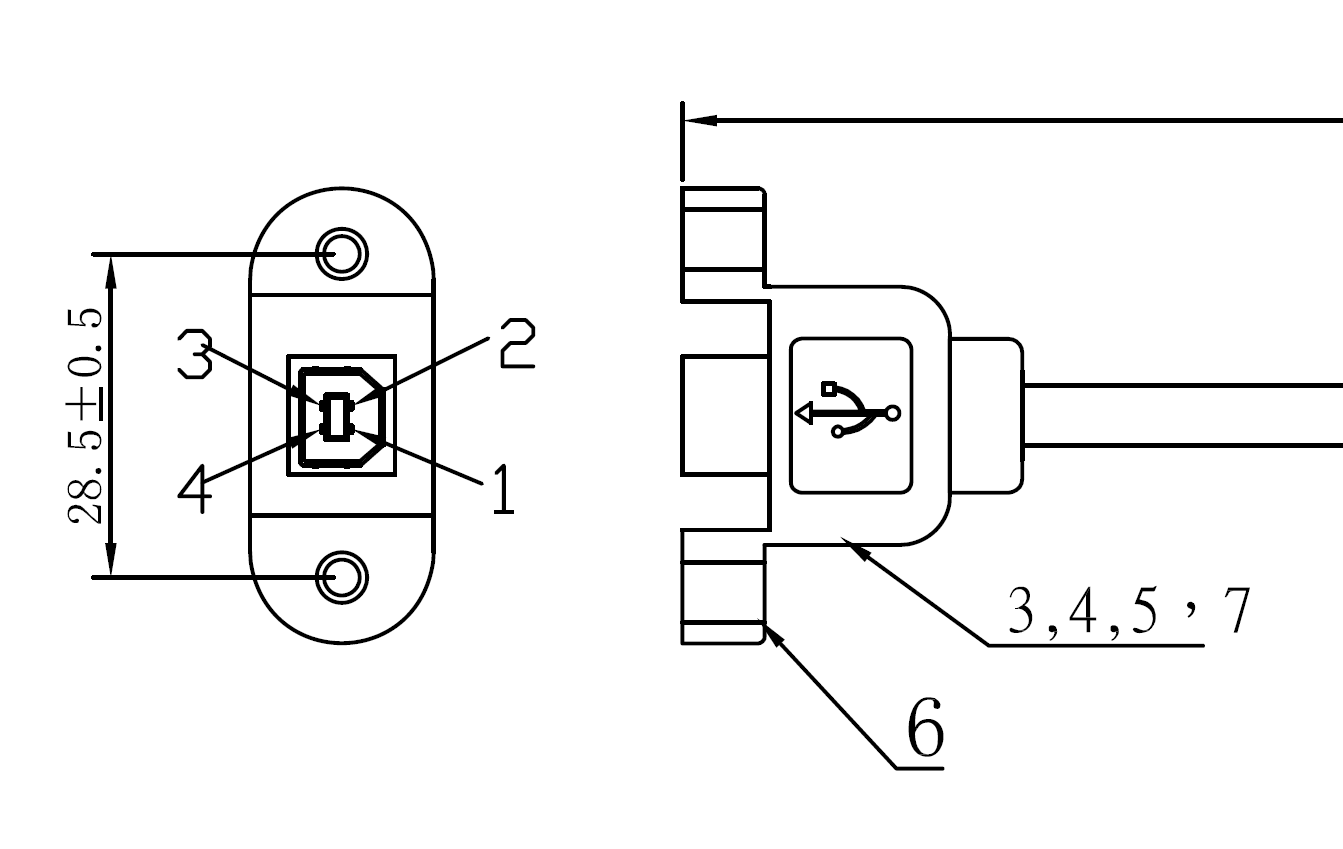
Duophonic/img/USB-panel.png
