svgeesus/EuroMPE/Duophonic/img/vref1-pos-RC-stable-then-not.png

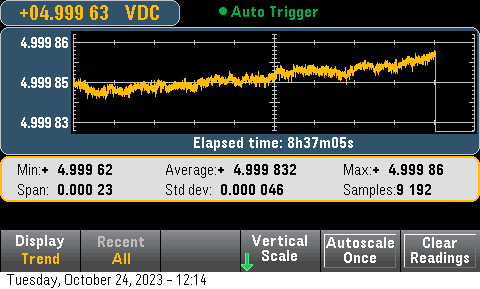
Duophonic/img/vref1-pos-RC-stable-then-not.png
