svgeesus/EuroMPE/Duophonic/img/vref2-pos-bad-as-ever.png

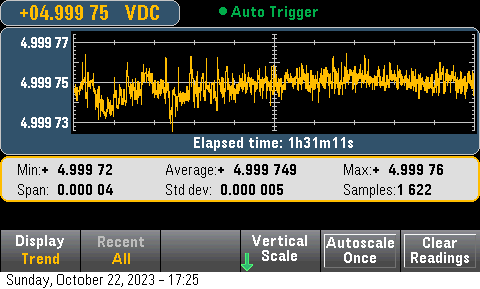
Duophonic/img/vref2-pos-bad-as-ever.png
