svgeesus/EuroMPE/Duophonic/img/vref2-pos-whoops.png

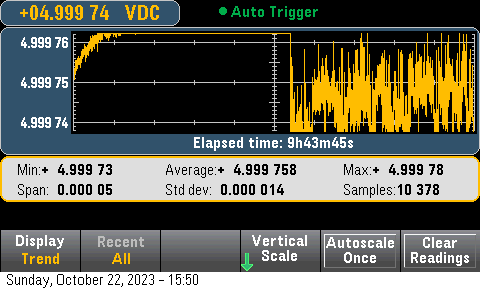
Duophonic/img/vref2-pos-whoops.png
