svgeesus/EuroMPE/Duophonic/img/vref--lt1236-board-v.01.png

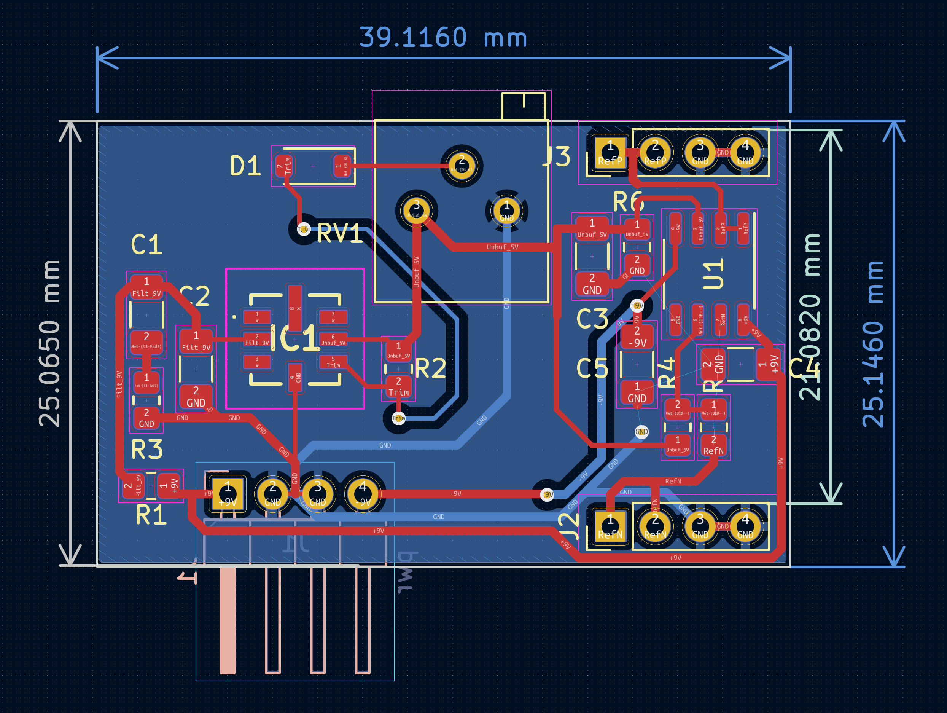
Duophonic/img/vref--lt1236-board-v.01.png
