svgeesus/EuroMPE/Duophonic/img/Zoli-1236-trim.png

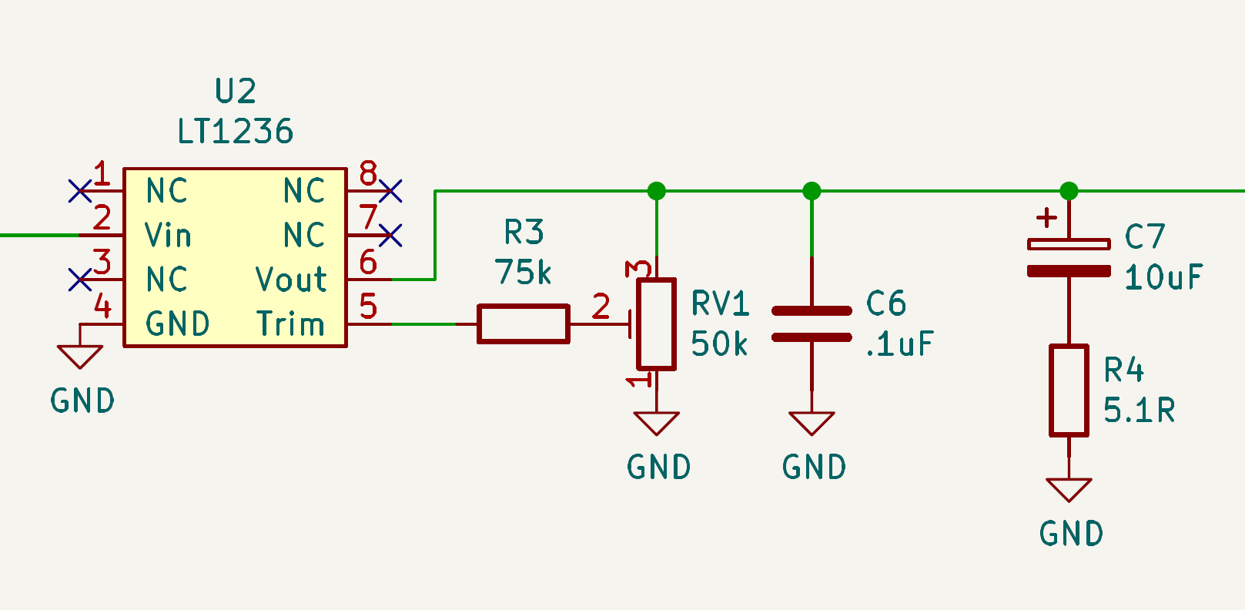
Duophonic/img/Zoli-1236-trim.png
