svgeesus/EuroMPE/img/4w-res.png

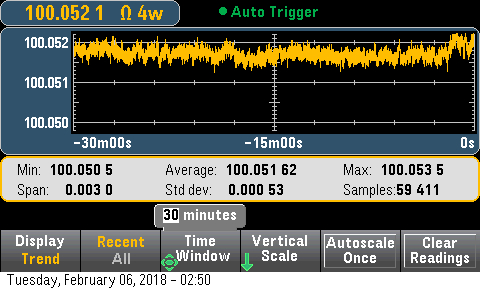
img/4w-res.png
