svgeesus/EuroMPE/img/AD588/5V-range3.png

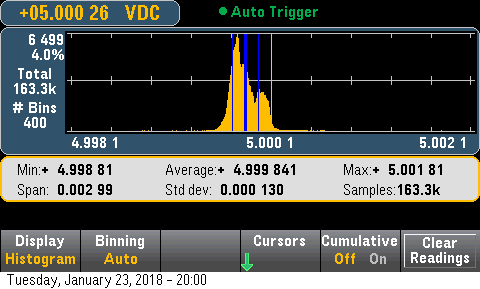
img/AD588/5V-range3.png
