svgeesus/EuroMPE/img/AD588/5V-range.png

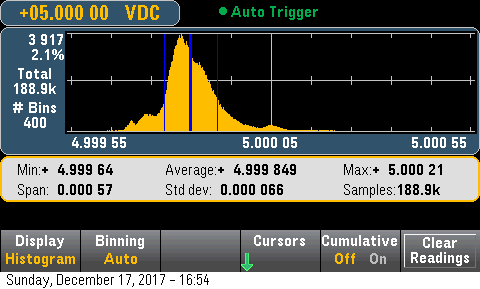
img/AD588/5V-range.png
