svgeesus/EuroMPE/img/AD588/5V-trimmed3.png

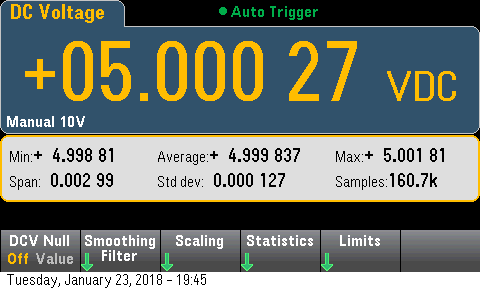
img/AD588/5V-trimmed3.png
