svgeesus/EuroMPE/img/AD588/5V-wandering4.png

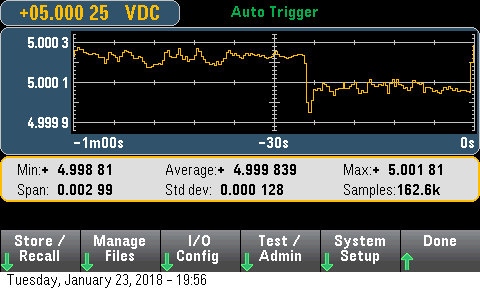
img/AD588/5V-wandering4.png
