svgeesus/EuroMPE/img/AD588/10V-range2.png

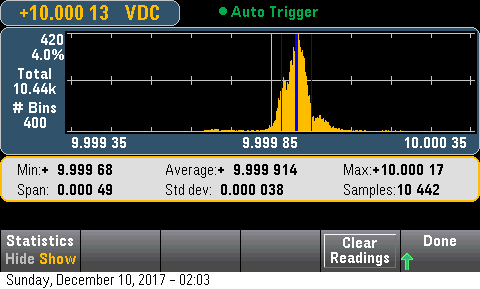
img/AD588/10V-range2.png
