svgeesus/EuroMPE/img/AD588/10V-range.png

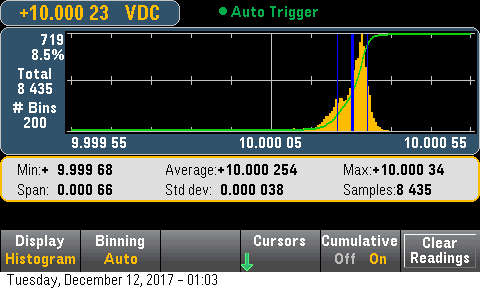
img/AD588/10V-range.png
