svgeesus/EuroMPE/img/AD588/10V-trimmed.png

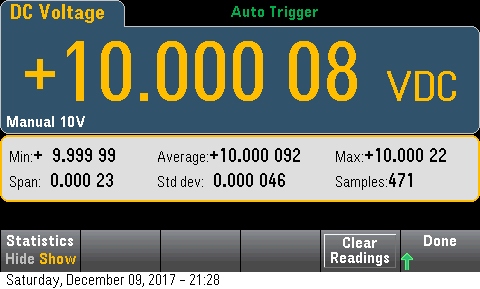
img/AD588/10V-trimmed.png
