svgeesus/EuroMPE/img/AD588/Untrimmed_10V_5V.png

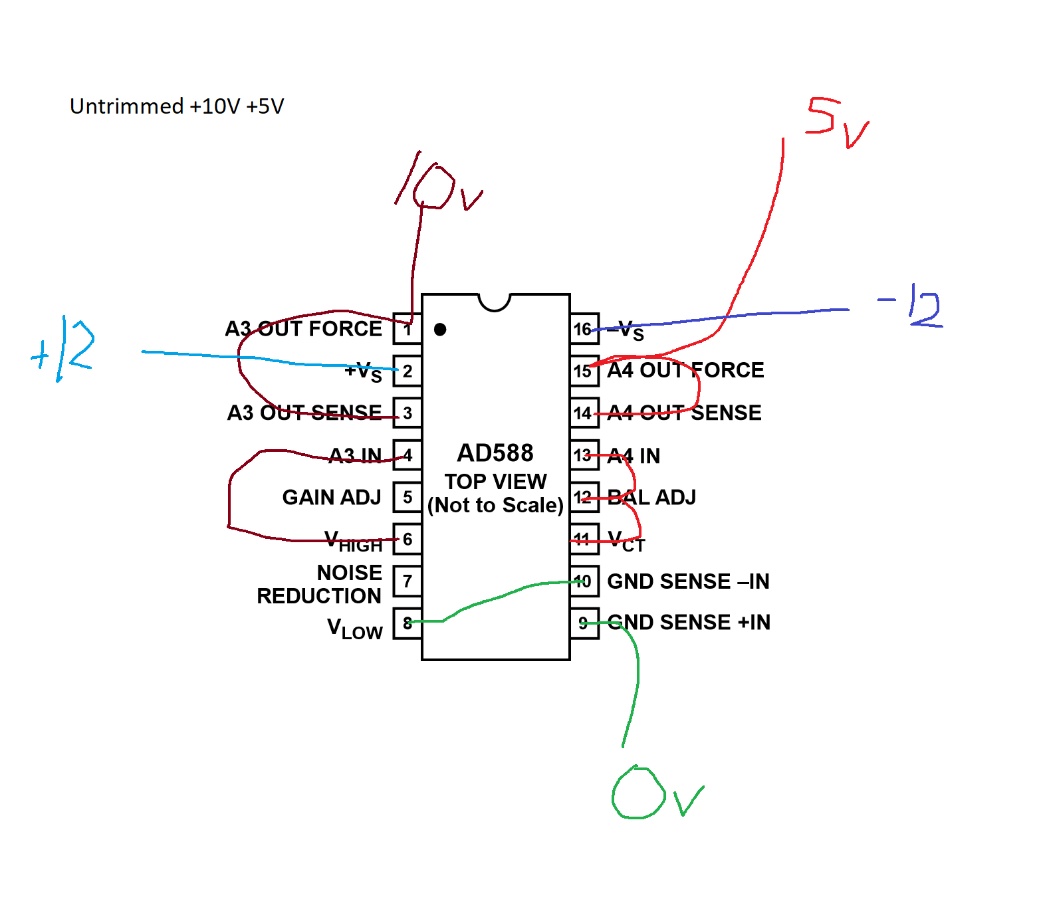
img/AD588/Untrimmed_10V_5V.png
