svgeesus/EuroMPE/img/alibaba.png

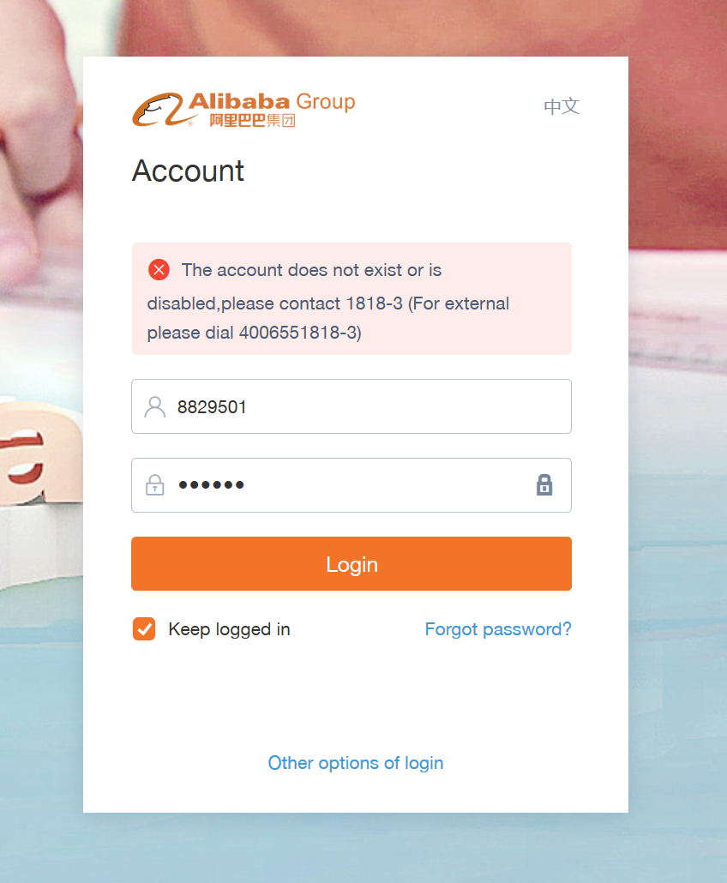
img/alibaba.png
