svgeesus/EuroMPE/img/DAC8168_data_input_register.png

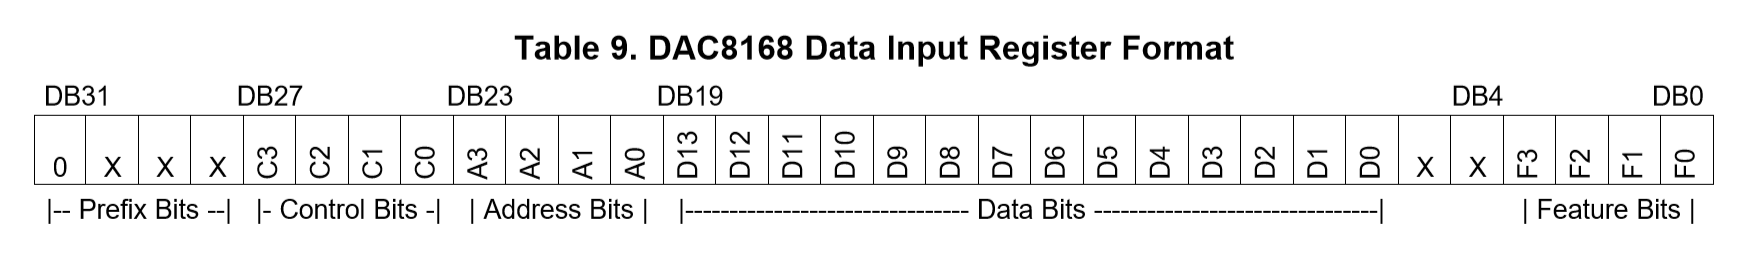
img/DAC8168_data_input_register.png
