svgeesus/EuroMPE/img/LM399/1.png

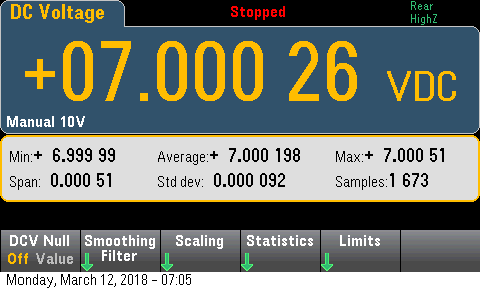
img/LM399/1.png
