svgeesus/EuroMPE/img/LM399/399-2-10V-hist.png

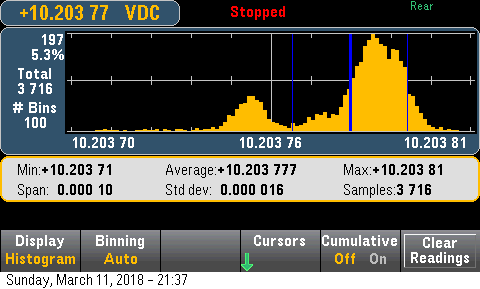
img/LM399/399-2-10V-hist.png
