svgeesus/EuroMPE/img/LM399/399-2-10v-Nov-2018-hist.png

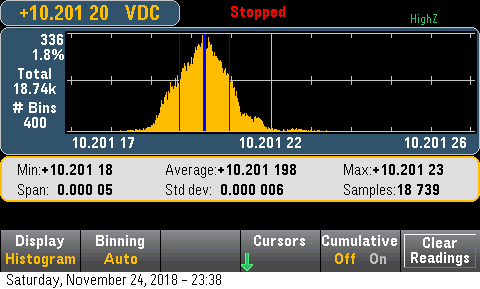
img/LM399/399-2-10v-Nov-2018-hist.png
