svgeesus/EuroMPE/img/LM399/399-2-10v-Nov-2018.png

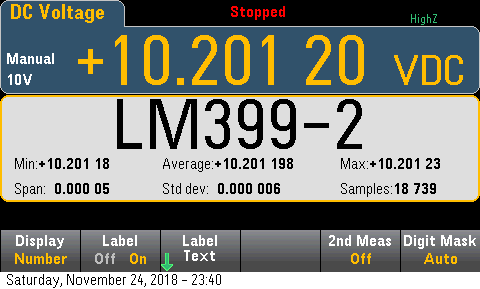
img/LM399/399-2-10v-Nov-2018.png
