svgeesus/EuroMPE/img/LM399/399-2-10V.png

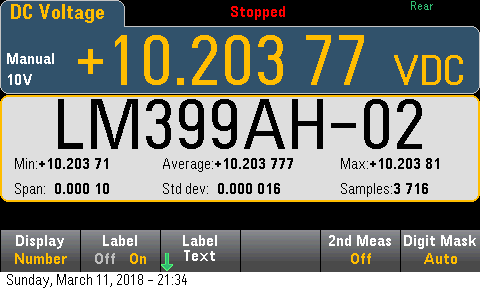
img/LM399/399-2-10V.png
