svgeesus/EuroMPE/img/LM399/399-2-Vz-30042018.png

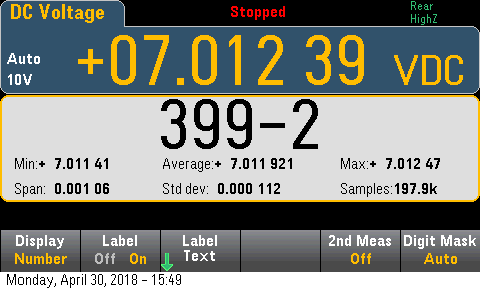
img/LM399/399-2-Vz-30042018.png
