svgeesus/EuroMPE/img/oscillators/SCREEN_5.png

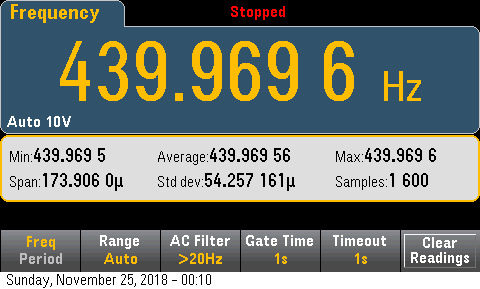
img/oscillators/SCREEN_5.png
