svgeesus/EuroMPE/img/oscillators/SCREEN_7.png

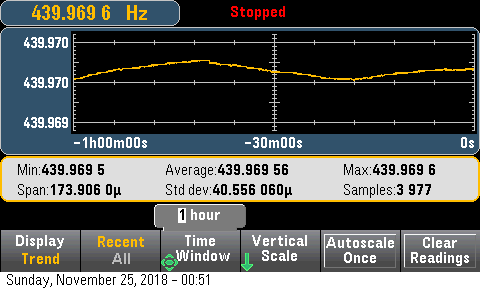
img/oscillators/SCREEN_7.png
