svgeesus/EuroMPE/img/oscillators/SCREEN_8.png

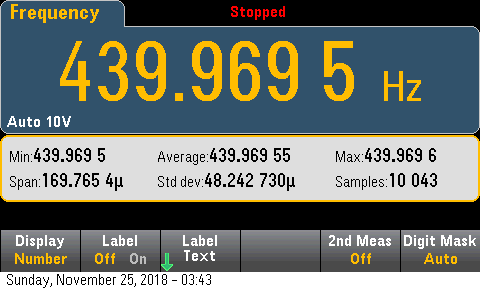
img/oscillators/SCREEN_8.png
