svgeesus/EuroMPE/img/other Vrefs/AD780-range.png

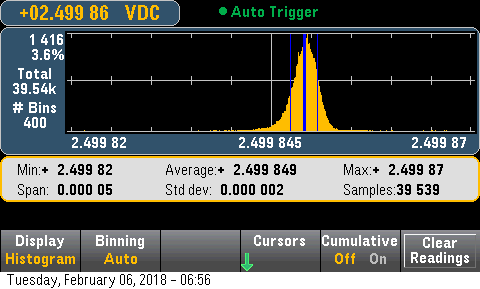
img/other Vrefs/AD780-range.png
