svgeesus/EuroMPE/img/other Vrefs/AD780-untrimmed.png

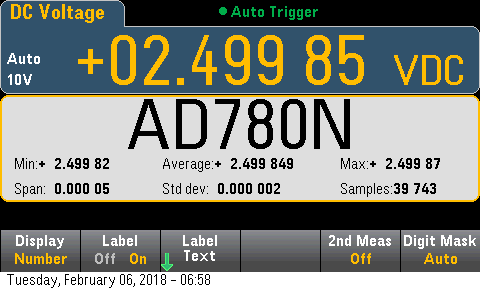
img/other Vrefs/AD780-untrimmed.png
