svgeesus/EuroMPE/img/other Vrefs/LT1021-Vref10.png

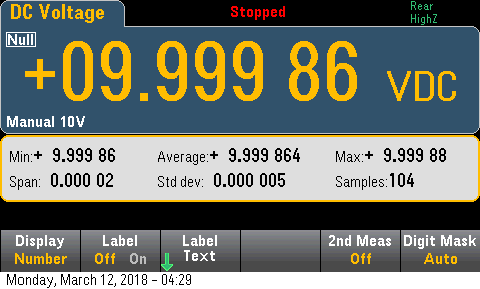
img/other Vrefs/LT1021-Vref10.png
