svgeesus/EuroMPE/img/other Vrefs/LT1021_Vref10_value.png

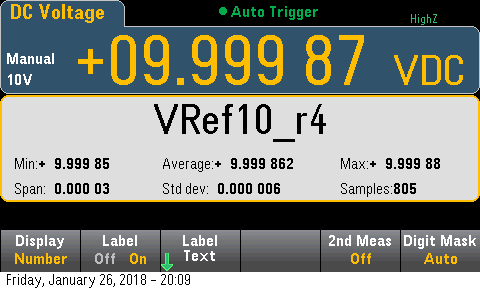
img/other Vrefs/LT1021_Vref10_value.png
