svgeesus/EuroMPE/img/Power/PS--12V.png

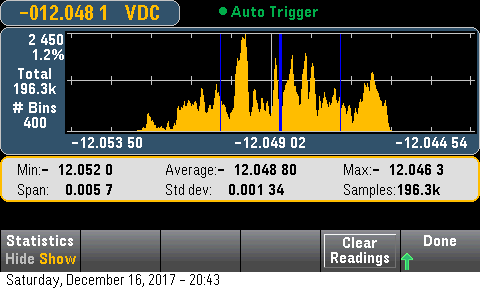
img/Power/PS--12V.png
