svgeesus/EuroMPE/img/Power/PS-AC-ripple.png

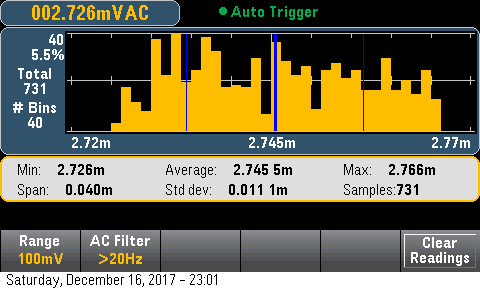
img/Power/PS-AC-ripple.png
