svgeesus/EuroMPE/img/Temperature/RT100-room-2.png

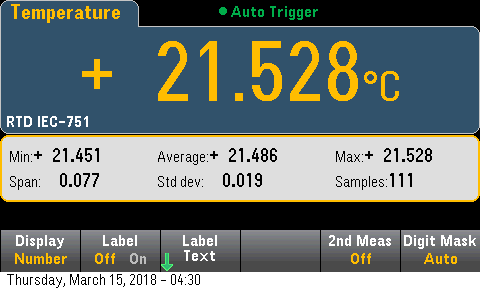
img/Temperature/RT100-room-2.png
