svgeesus/EuroMPE/img/Temperature/TypeK-room.png

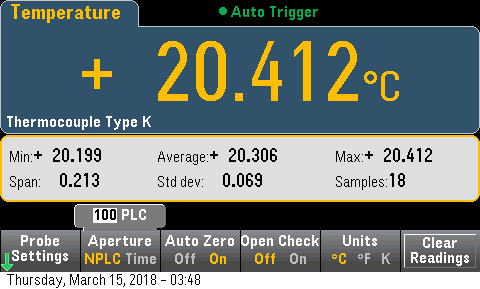
img/Temperature/TypeK-room.png
