svgeesus/EuroMPE/Duophonic/img/adafruit_products_0-91_STEMMA_OLED_fab_print.png

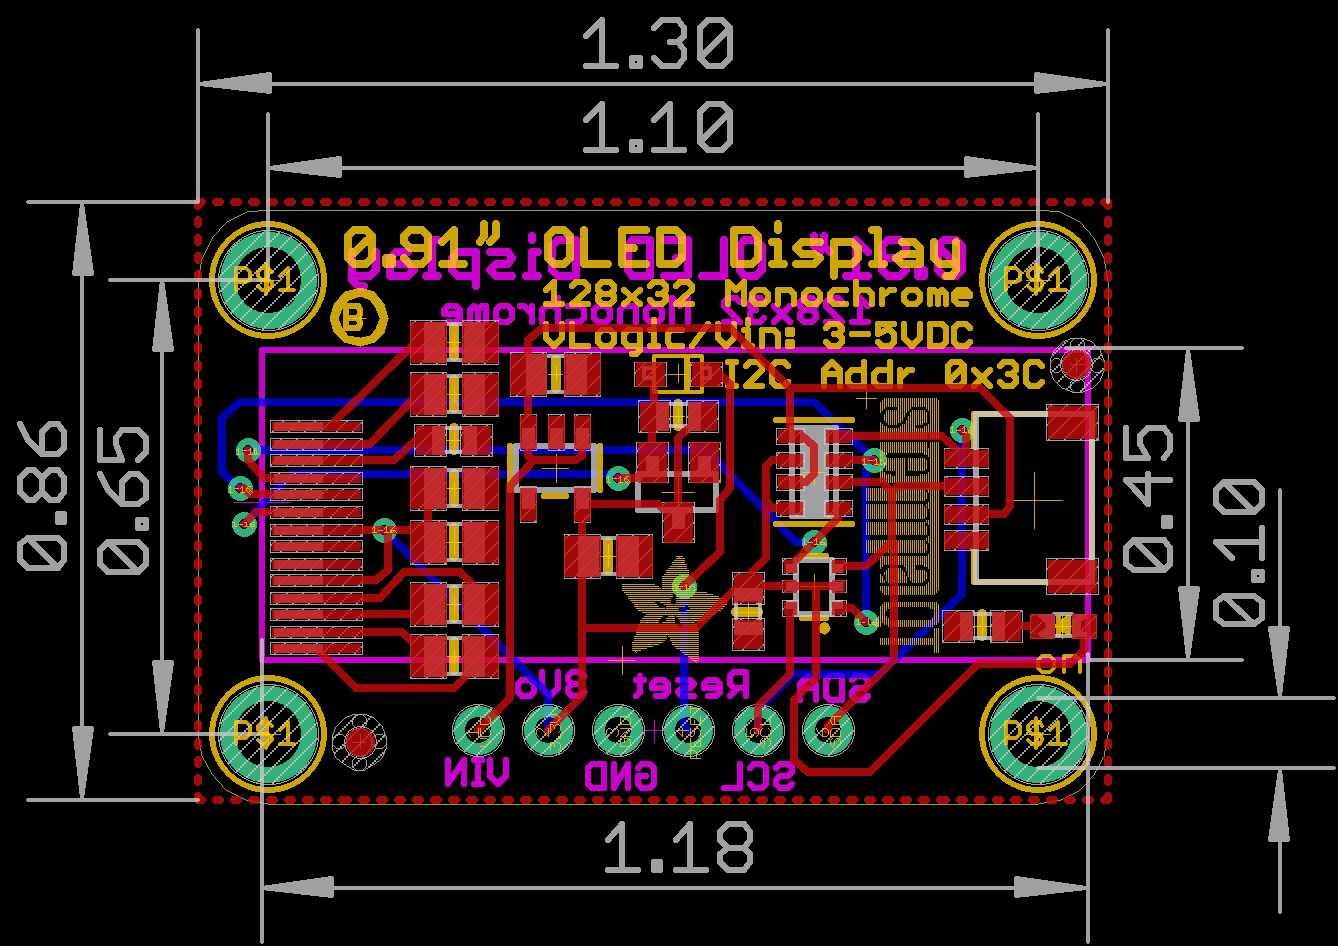
Duophonic/img/adafruit_products_0-91_STEMMA_OLED_fab_print.png
