svgeesus/EuroMPE/Duophonic/img/adafruit_products_0-96in_OLED_fab_print.png

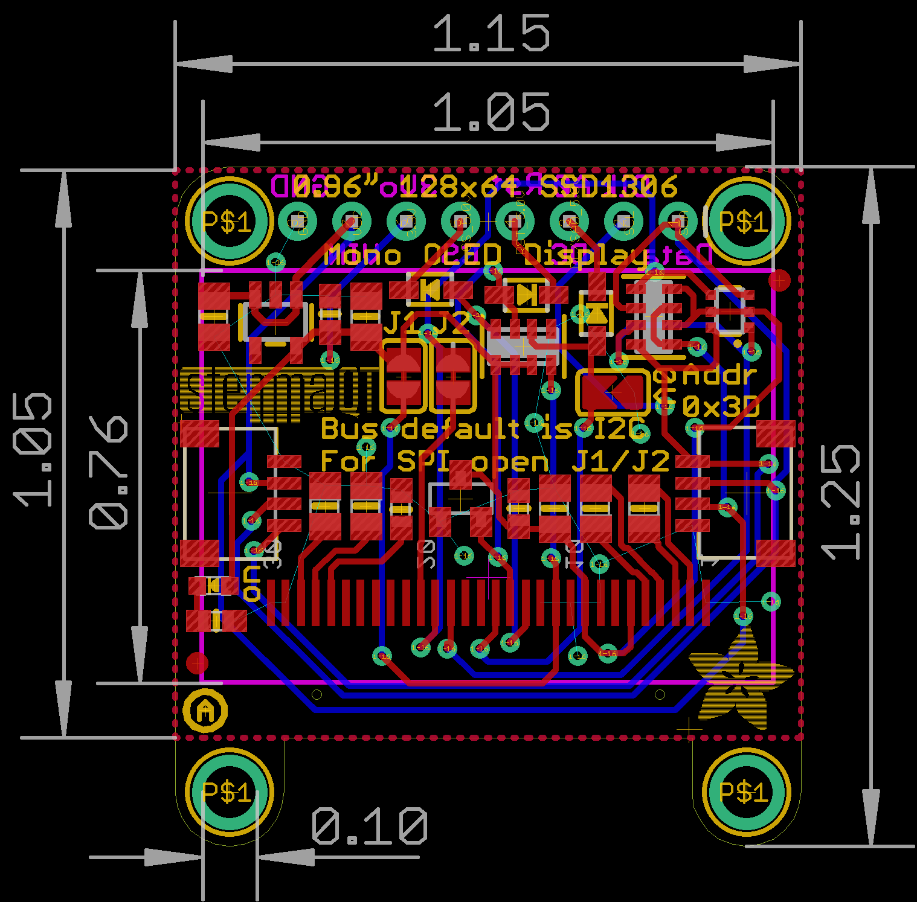
Duophonic/img/adafruit_products_0-96in_OLED_fab_print.png
