svgeesus/EuroMPE/code/seaboard_usbhost_test001.txt

USB Host MIDI Testing
Control Change, ch=9, control=74, value=64
Pitchbend, ch=9, pitchbend=0
Note On, ch=9, note=43, velocity=18
Pitchbend, ch=9, pitchbend=0
Pitchbend, ch=9, pitchbend=0
Note On, ch=9, note=43, velocity=18
Channel Aftertouch, ch=9, pressure=127
Pitchbend, ch=9, pitchbend=0
Note On, ch=9, note=43, velocity=18
Channel Aftertouch, ch=9, pressure=125
Pitchbend, ch=9, pitchbend=-17
Note On, ch=9, note=43, velocity=18
Channel Aftertouch, ch=9, pressure=123
Pitchbend, ch=9, pitchbend=-17
Note On, ch=9, note=43, velocity=18
Pitchbend, ch=9, pitchbend=2
Pitchbend, ch=9, pitchbend=-17
Note On, ch=9, note=43, velocity=18
Channel Aftertouch, ch=9, pressure=121
Pitchbend, ch=9, pitchbend=-17
Note On, ch=9, note=43, velocity=18
Channel Aftertouch, ch=9, pressure=119
Pitchbend, ch=9, pitchbend=-17
Note On, ch=9, note=43, velocity=18
Pitchbend, ch=9, pitchbend=0
Pitchbend, ch=9, pitchbend=-17
Note On, ch=9, note=43, velocity=18
Channel Aftertouch, ch=9, pressure=117
Pitchbend, ch=9, pitchbend=-17
Note On, ch=9, note=43, velocity=18
Channel Aftertouch, ch=9, pressure=115
Pitchbend, ch=9, pitchbend=-17
Note On, ch=9, note=43, velocity=18
Channel Aftertouch, ch=9, pressure=113
Pitchbend, ch=9, pitchbend=-17
Note On, ch=9, note=43, velocity=18
Note Off, ch=9, note=43, release velocity=30
Pitchbend, ch=9, pitchbend=-17
Note On, ch=9, note=43, velocity=18
Control Change, ch=9, control=74, value=64
Pitchbend, ch=9, pitchbend=0
Note On, ch=9, note=48, velocity=20
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
Sysex, of length=6 now complete
Control Change, ch=9, control=99, value=0
Control Change, ch=9, control=98, value=2
Control Change, ch=9, control=6, value=4
Control Change, ch=9, control=6, value=3
Control Change, ch=9, control=98, value=2
Control Change, ch=9, control=6, value=4
Program Change, ch=9, patch number=2
Control Change, ch=9, control=98, value=2
Control Change, ch=9, control=6, value=4
Program Change, ch=9, patch number=3
Control Change, ch=9, control=98, value=2
Control Change, ch=9, control=6, value=4
