svgeesus/EuroMPE/Duophonic/img/tune-in-2.png

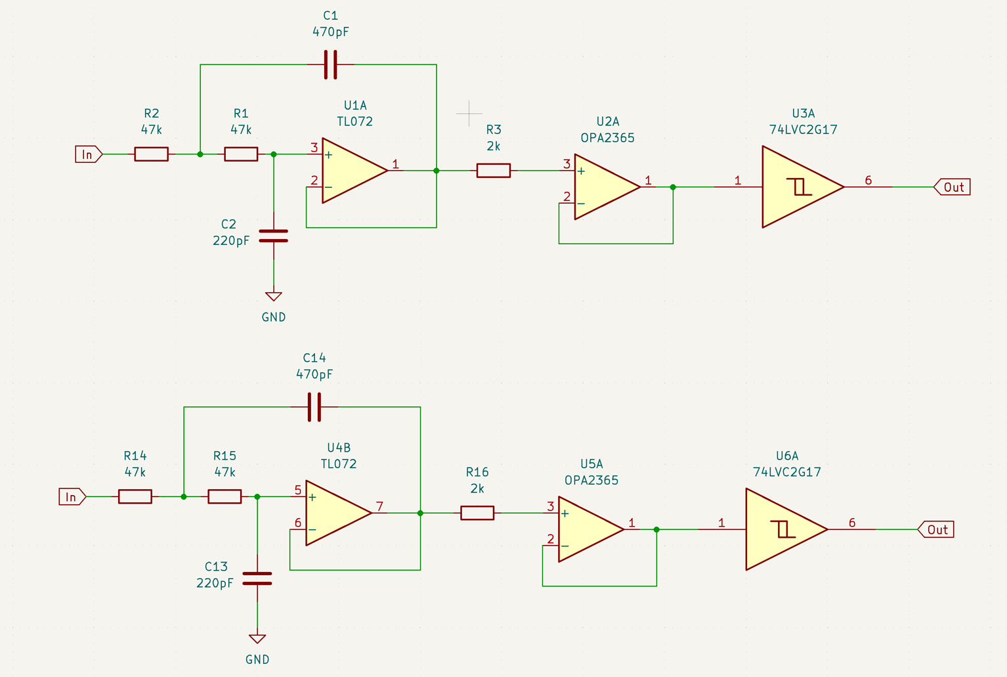
Duophonic/img/tune-in-2.png
