svgeesus/EuroMPE/Duophonic/img/tune-in-bottom.png

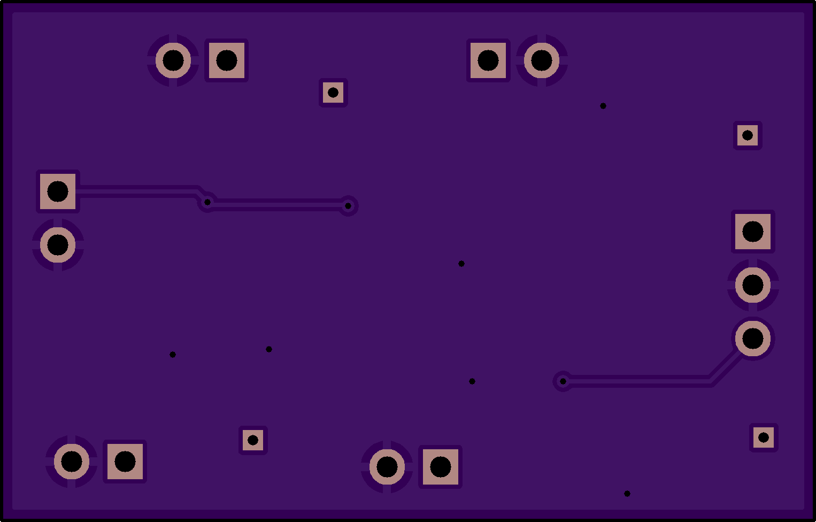
Duophonic/img/tune-in-bottom.png
