svgeesus/EuroMPE/Duophonic/img/tune-in-top.png

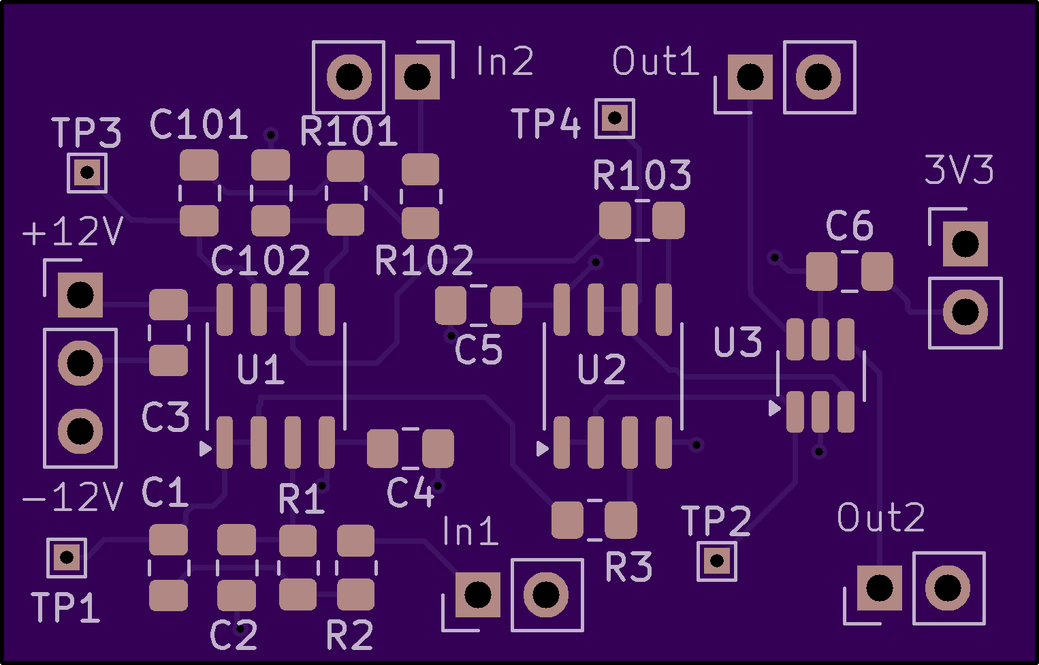
Duophonic/img/tune-in-top.png
