svgeesus/EuroMPE/Duophonic/KiCad/MPU-test/MPU-test-allgrey.png

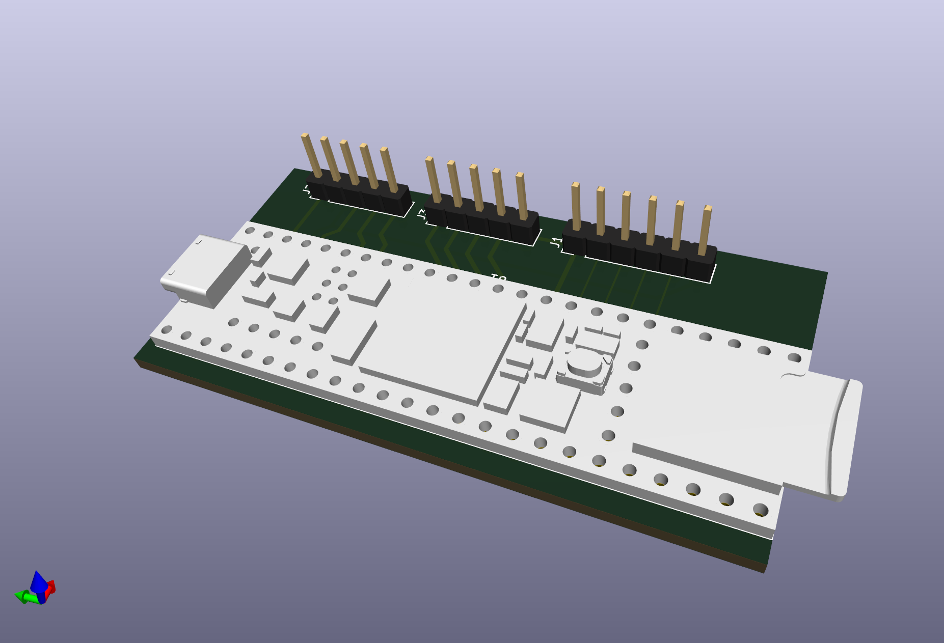
Duophonic/KiCad/MPU-test/MPU-test-allgrey.png
