svgeesus/EuroMPE/Duophonic/KiCad/MPU-test/MPU-test-back.png

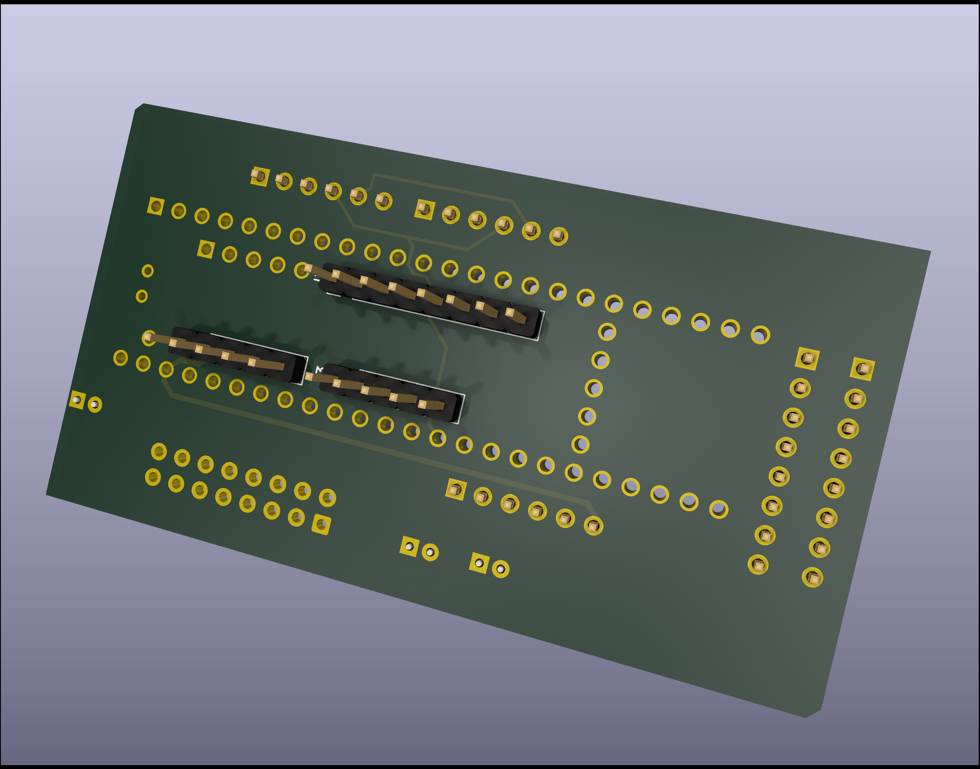
Duophonic/KiCad/MPU-test/MPU-test-back.png
