svgeesus/EuroMPE/Duophonic/KiCad/MPU-test/MPU-test.png

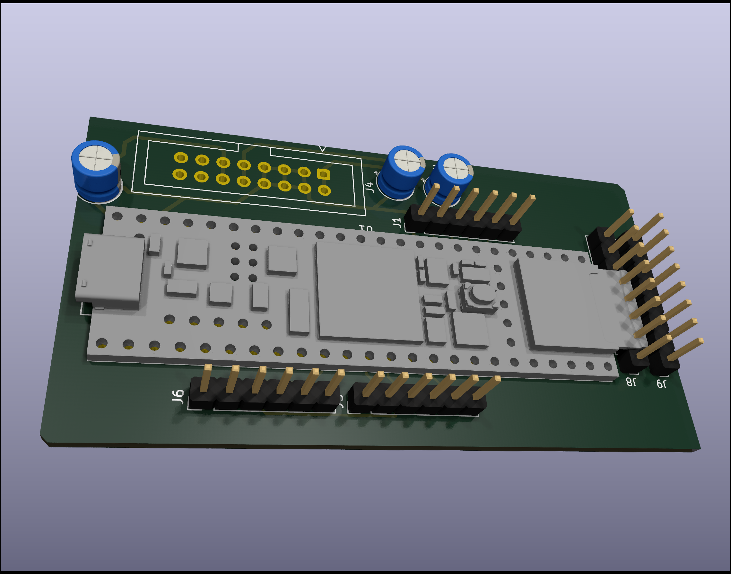
Duophonic/KiCad/MPU-test/MPU-test.png
