svgeesus/EuroMPE/Duophonic/vref-board.pdf

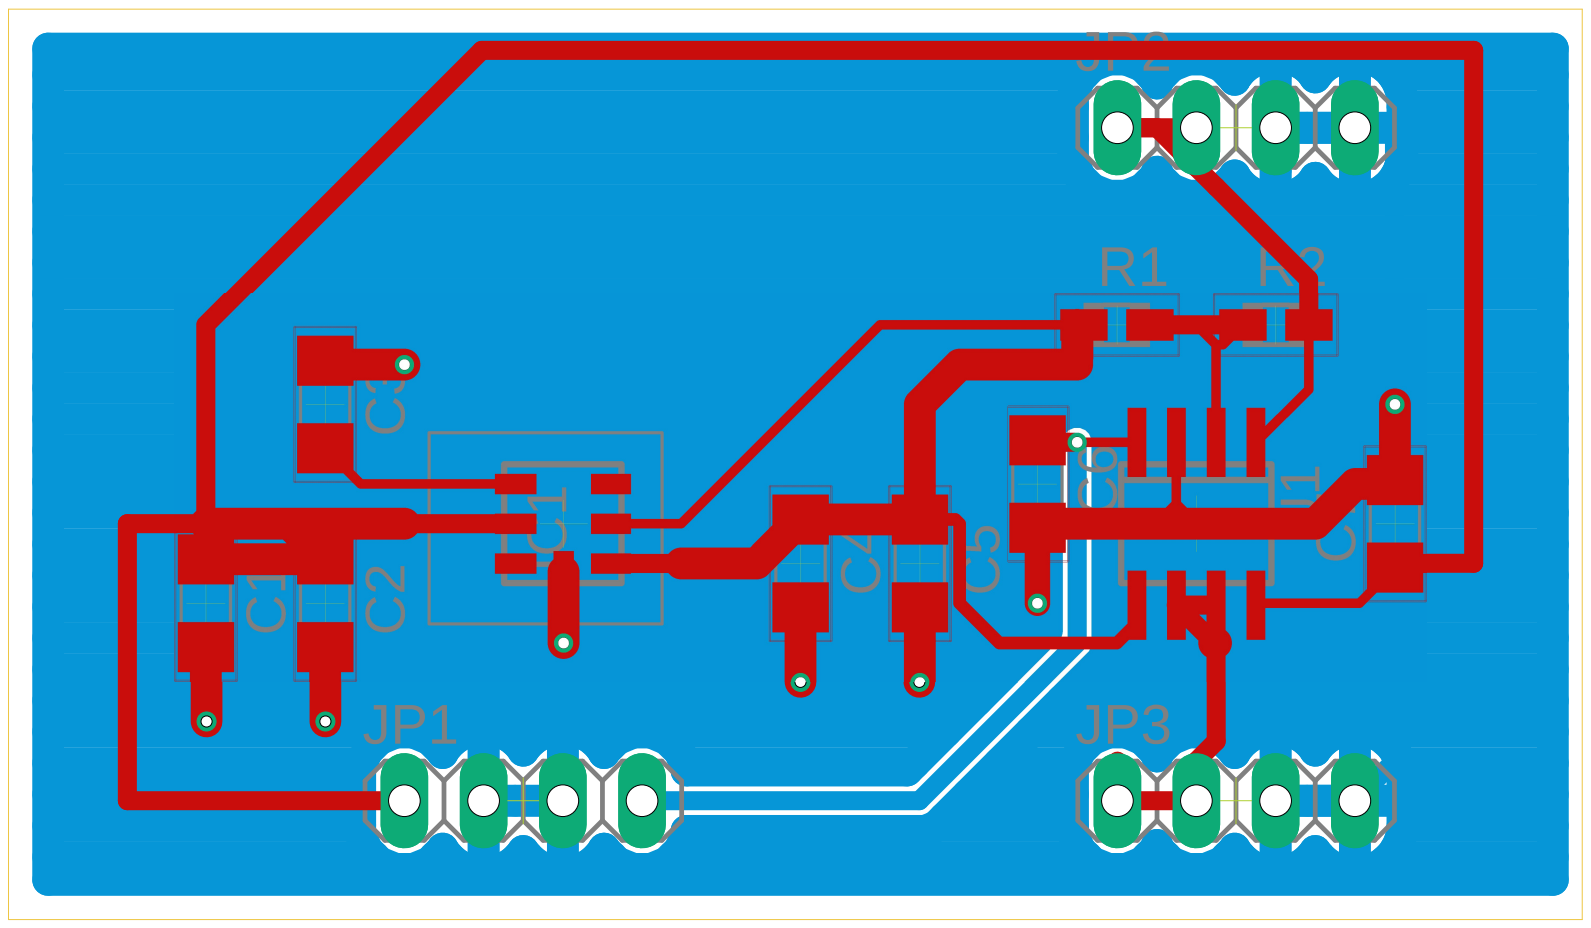
[picture p285: page 1]
