svgeesus/EuroMPE/Duophonic/pitchdac-schematic-v03.pdf

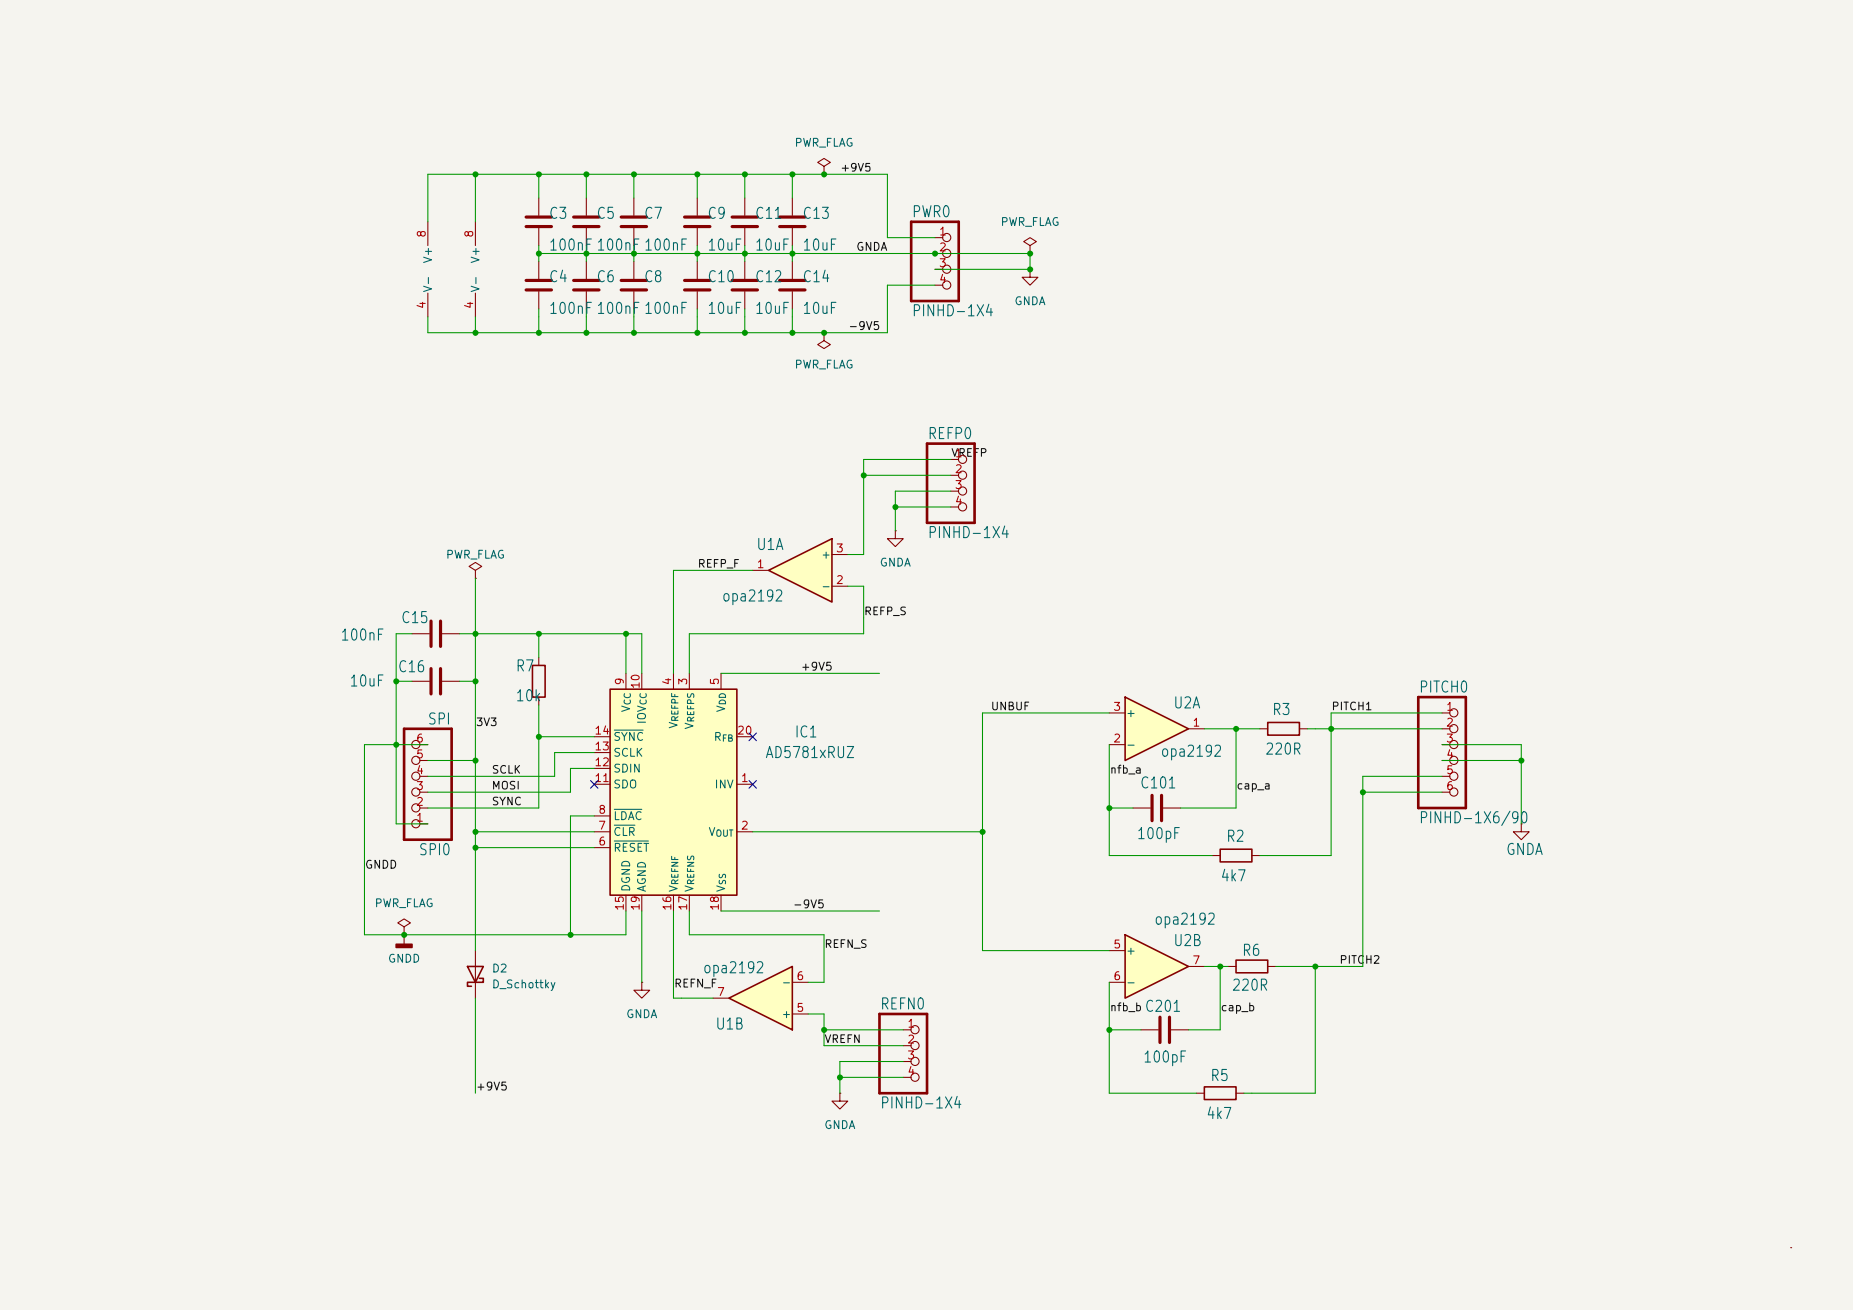
[picture p286: page 1]
