svgeesus/EuroMPE/Duophonic/pitchdac-schematic.pdf

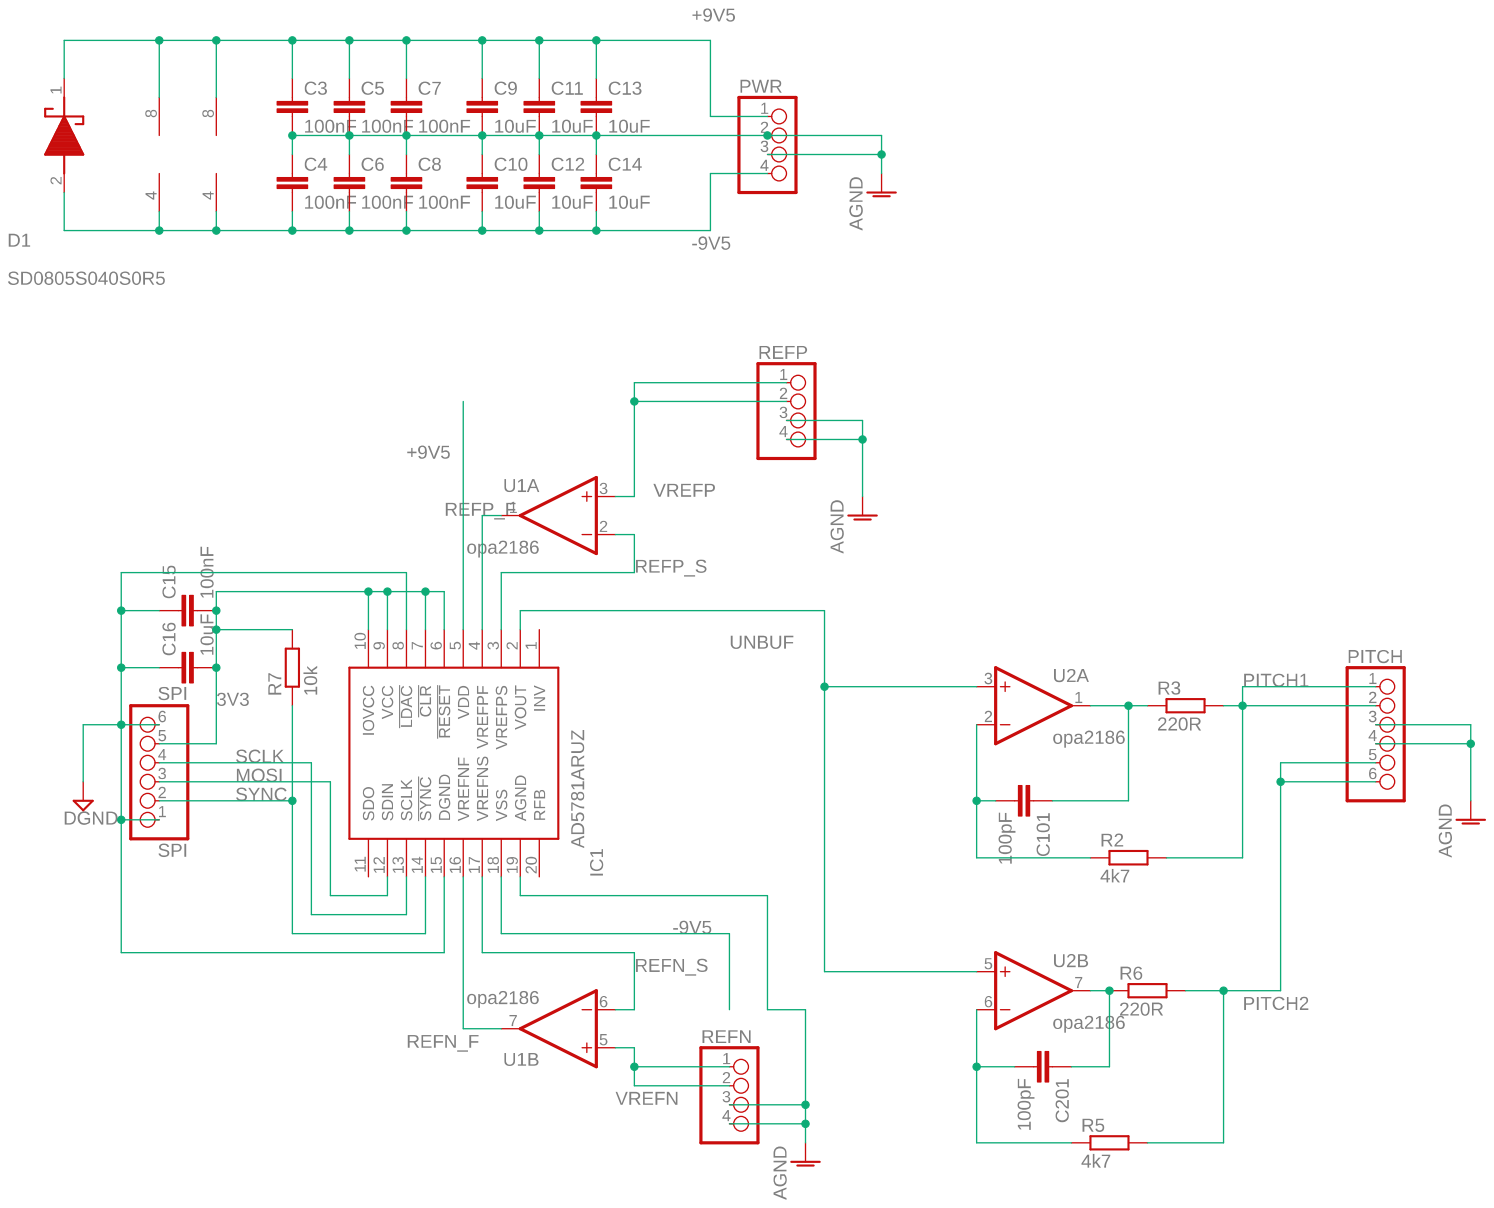
[picture p287: page 1]
